Tbo-s/sya_ai-scanner/3D_files/structure/tandwiel(small).stl

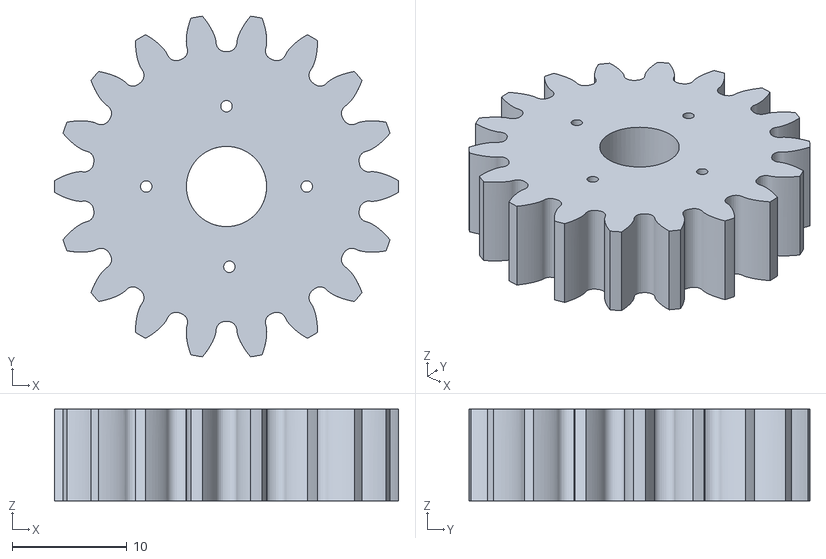
[picture p15: CAD file, 2026-03-24]
3D_files/structure/tandwiel(small).stl
30.0 x 29.7 x 8.00
