Tbo-s/sya_ai-scanner/3D_files/ARM/arm-part3.stl

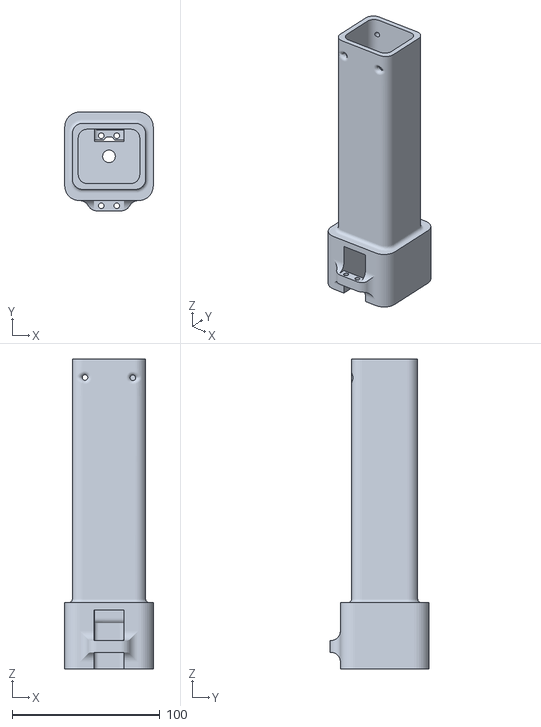
[picture p16: CAD file, 2026-03-13]
3D_files/ARM/arm-part3.stl
60.0 x 67.0 x 210.0
