Tbo-s/sya_ai-scanner/3D_files/gate/gate-motor.stl

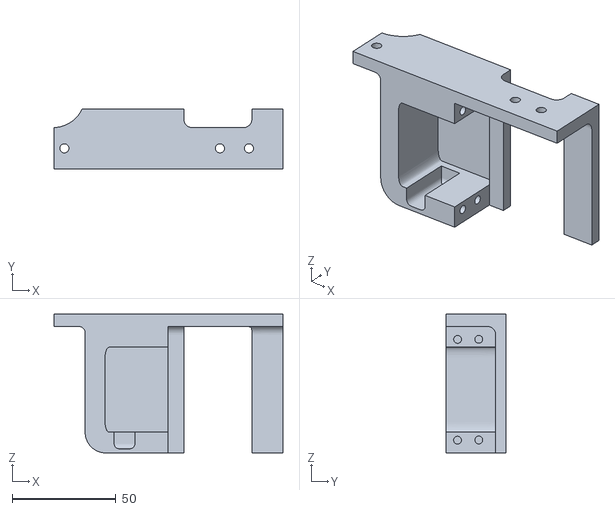
[picture p17: CAD file, 2026-03-03]
3D_files/gate/gate-motor.stl
110.4 x 29.0 x 67.0
