Tbo-s/sya_ai-scanner/3D_files/part-casings/picam.stl

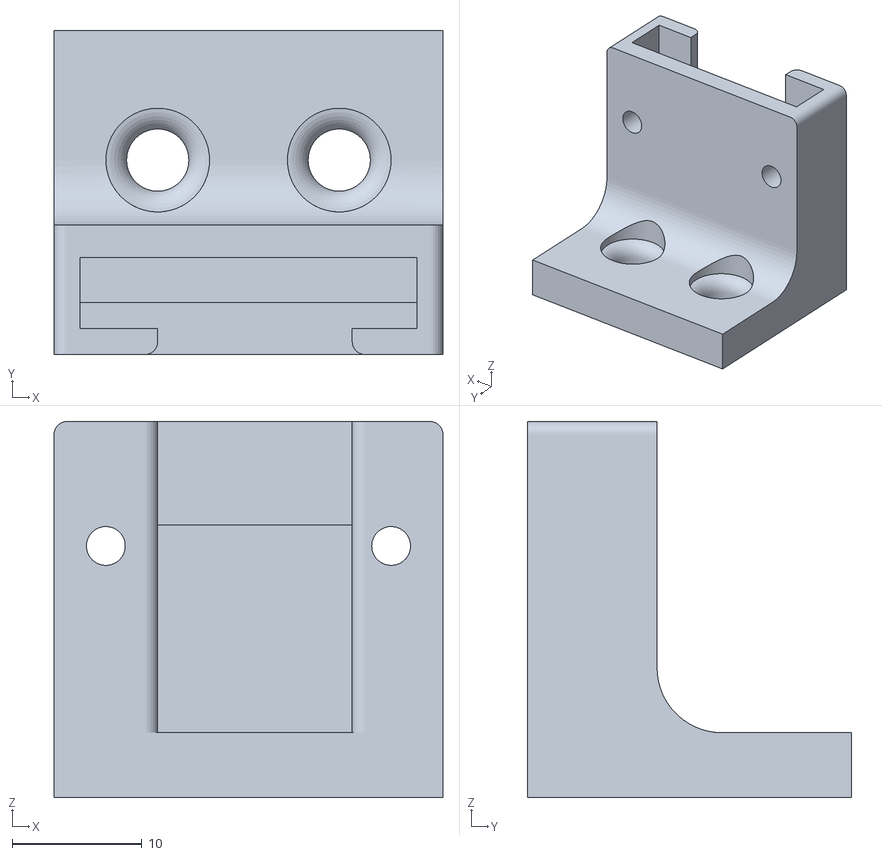
[picture p18: CAD file, 2026-03-13]
3D_files/part-casings/picam.stl
30.0 x 25.0 x 29.0
