Tbo-s/sya_ai-scanner/3D_files/structure/2020brackets.stl

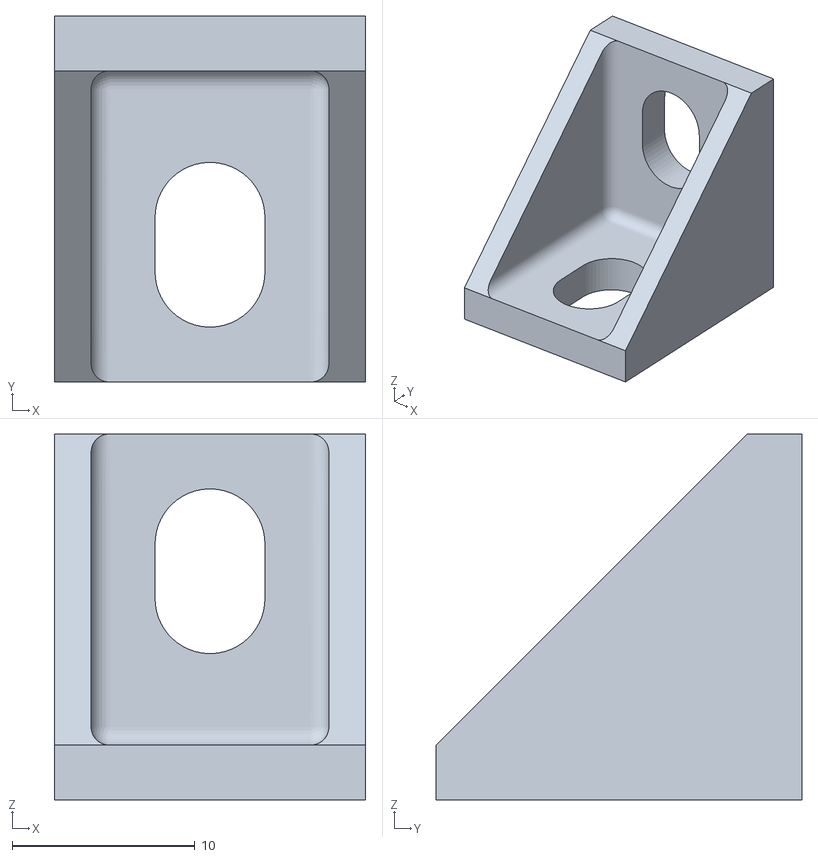
[picture p19: CAD file, 2026-03-09]
3D_files/structure/2020brackets.stl
17.0 x 20.0 x 20.0
