Tbo-s/sya_ai-scanner/3D_files/xy-parts/x-carry3-Right.stl

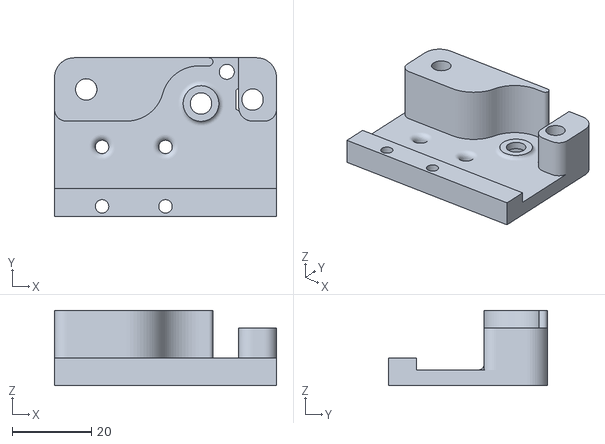
[picture p20: CAD file, 2026-03-04]
3D_files/xy-parts/x-carry3-Right.stl
56.0 x 40.0 x 19.0
