Tbo-s/sya_ai-scanner/3D_files/ARM/arm-part6.stl

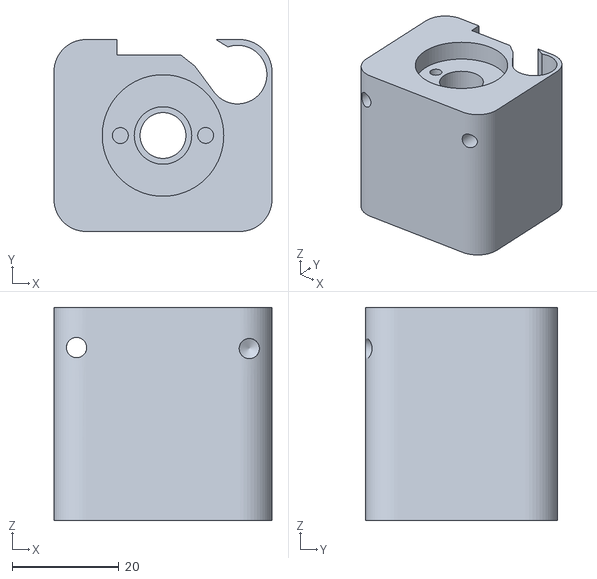
[picture p21: CAD file, 2026-03-03]
3D_files/ARM/arm-part6.stl
40.9 x 36.0 x 40.0
