Tbo-s/sya_ai-scanner/3D_files/gate/gate-part1.stl

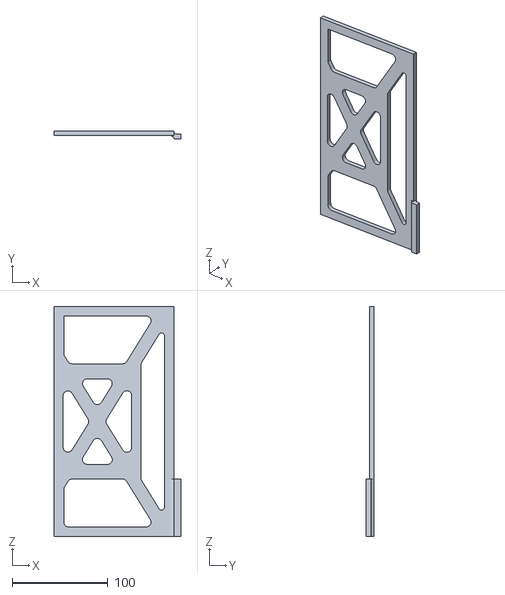
[picture p22: CAD file, 2026-03-03]
3D_files/gate/gate-part1.stl
132.0 x 8.60 x 240.0
