Tbo-s/sya_ai-scanner/3D_files/part-casings/mega_top.stl

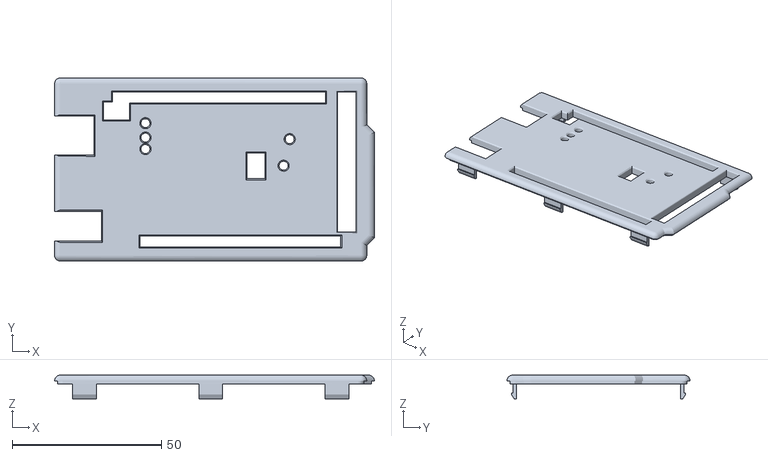
[picture p23: CAD file, 2026-03-10]
3D_files/part-casings/mega_top.stl
107.1 x 61.3 x 8.00
