Tbo-s/sya_ai-scanner/3D_files/structure/LED-holder-right_(3X).stl

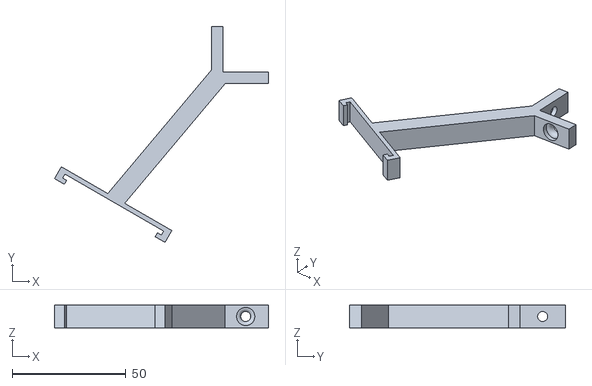
[picture p24: CAD file, 2026-03-03]
3D_files/structure/LED-holder-right_(3X).stl
93.9 x 94.7 x 10.0
