Tbo-s/sya_ai-scanner/3D_files/ARM/arm-part1.stl

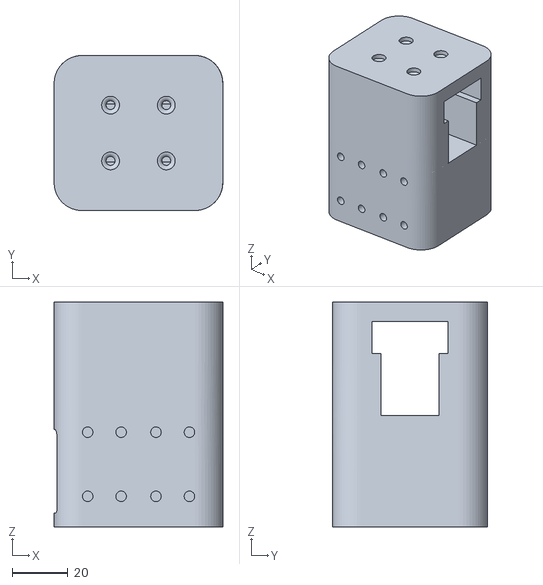
[picture p25: CAD file, 2026-03-03]
3D_files/ARM/arm-part1.stl
60.5 x 55.6 x 80.7
