Tbo-s/sya_ai-scanner/3D_files/part-casings/Leonardo_bottem.stl

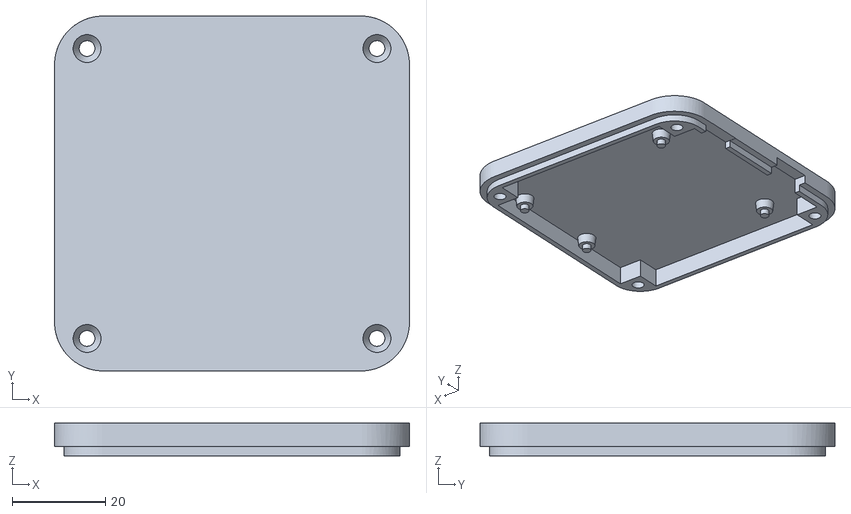
[picture p26: CAD file, 2026-03-10]
3D_files/part-casings/Leonardo_bottem.stl
76.3 x 76.3 x 7.00
