Tbo-s/sya_ai-scanner/3D_files/xy-parts/nema17_holder_right.stl

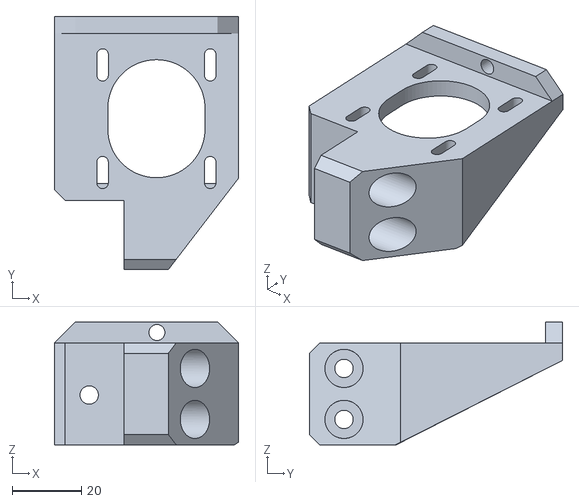
[picture p27: CAD file, 2026-03-03]
3D_files/xy-parts/nema17_holder_right.stl
53.0 x 73.0 x 35.4
