Tbo-s/sya_ai-scanner/3D_files/ARM/arm-part2.stl

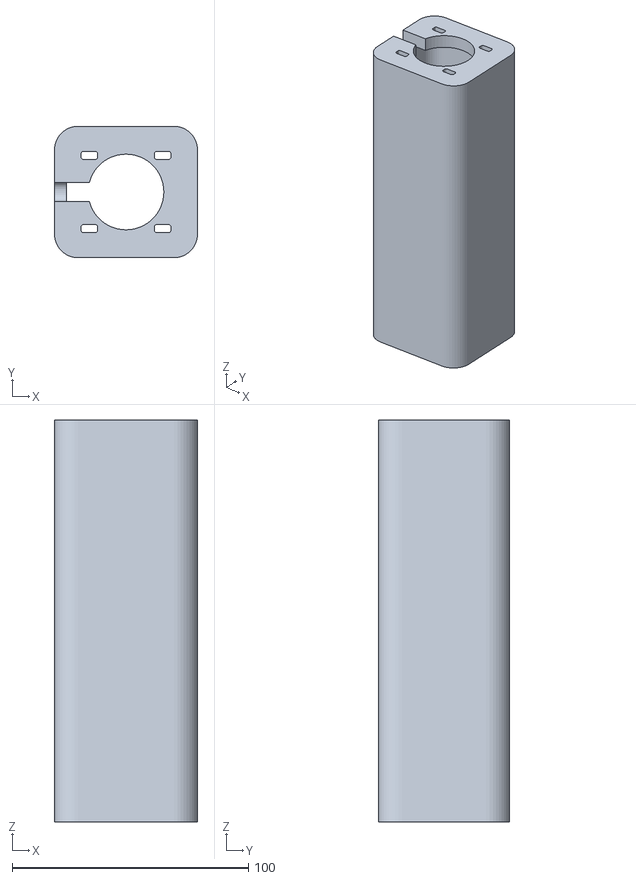
[picture p28: CAD file, 2026-03-03]
3D_files/ARM/arm-part2.stl
60.5 x 55.6 x 170.0
