Tbo-s/sya_ai-scanner/3D_files/gate/gate-part5.stl

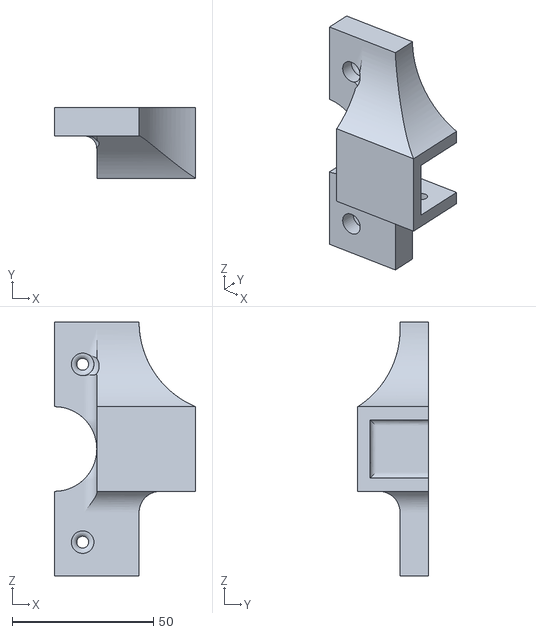
[picture p29: CAD file, 2026-03-03]
3D_files/gate/gate-part5.stl
50.0 x 25.0 x 90.0
