Tbo-s/sya_ai-scanner/3D_files/part-casings/pi_bottem.stl

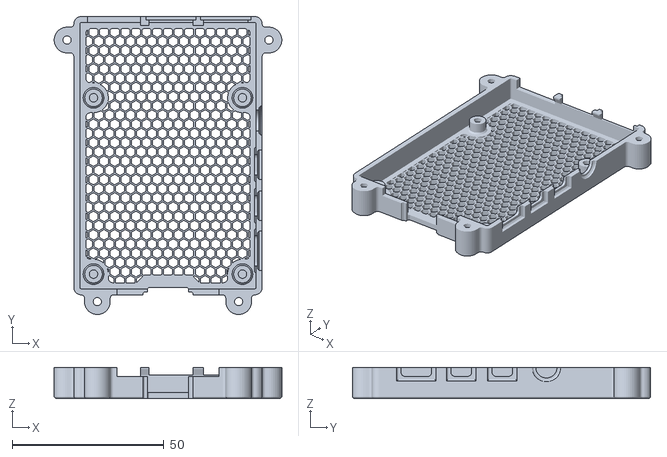
[picture p30: CAD file, 2026-03-10]
3D_files/part-casings/pi_bottem.stl
74.9 x 98.0 x 10.3
