Tbo-s/sya_ai-scanner/3D_files/structure/tandwiel_mg996R_(2X).stl

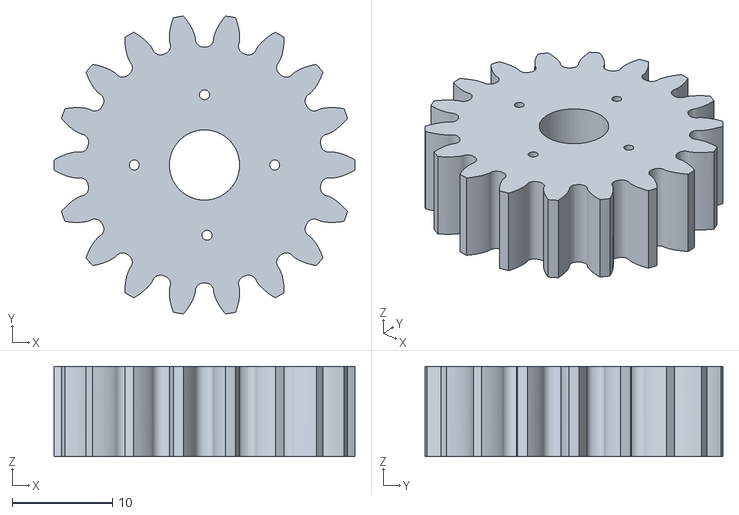
[picture p31: CAD file, 2026-03-03]
3D_files/structure/tandwiel_mg996R_(2X).stl
30.0 x 29.7 x 9.00
