Tbo-s/sya_ai-scanner/3D_files/xy-parts/idler_mount_left.stl

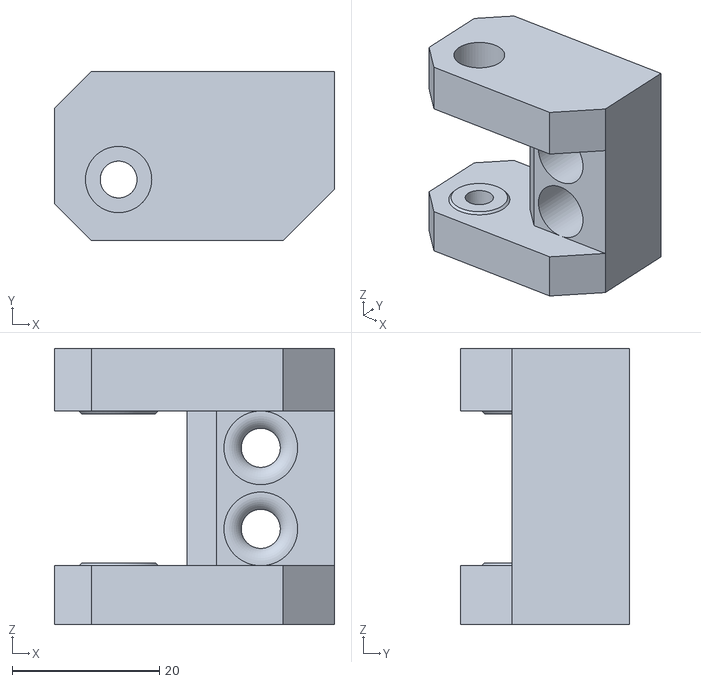
[picture p32: CAD file, 2026-03-03]
3D_files/xy-parts/idler_mount_left.stl
38.0 x 23.0 x 37.5
