Tbo-s/sya_ai-scanner/3D_files/ARM/arm-part7(4X).stl

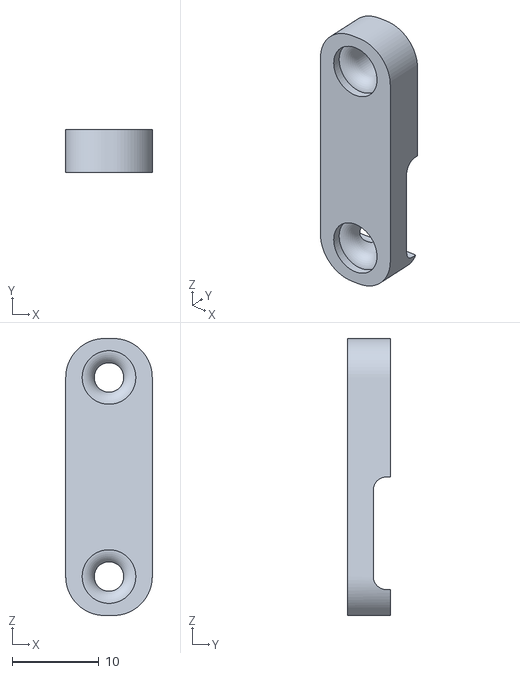
[picture p33: CAD file, 2026-03-03]
3D_files/ARM/arm-part7(4X).stl
10.0 x 5.00 x 32.0
