Tbo-s/sya_ai-scanner/3D_files/gate/gate-motor-adapter.stl

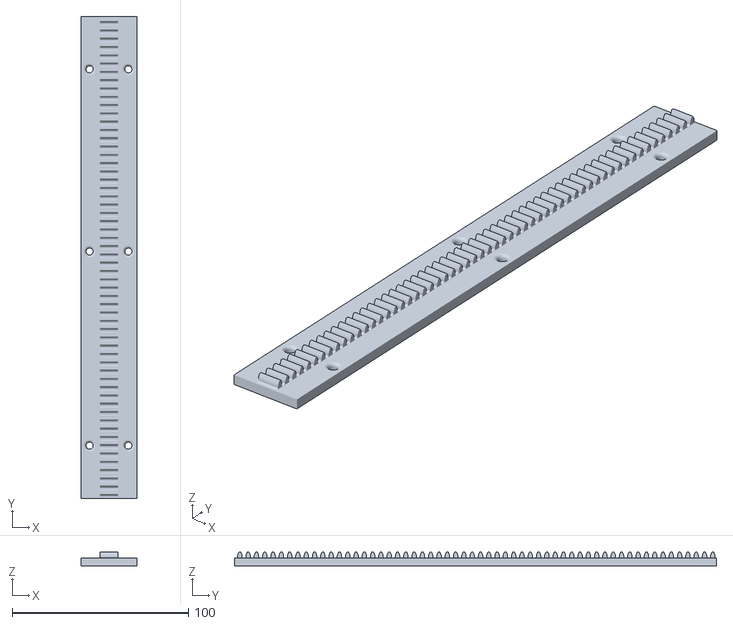
[picture p34: CAD file, 2026-03-03]
3D_files/gate/gate-motor-adapter.stl
32.0 x 273.8 x 7.80
