Tbo-s/sya_ai-scanner/3D_files/part-casings/switch.stl

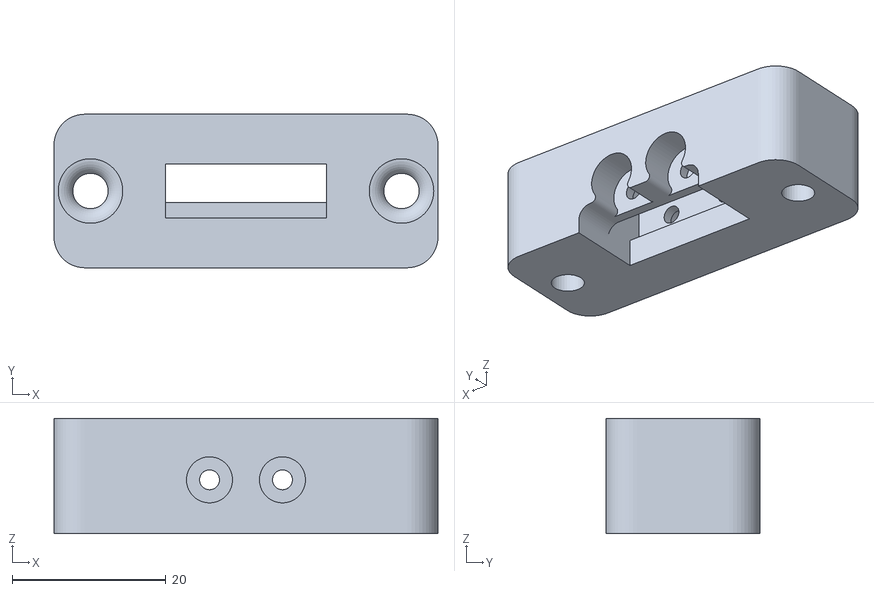
[picture p35: CAD file, 2026-03-10]
3D_files/part-casings/switch.stl
50.0 x 20.0 x 15.0
