Tbo-s/sya_ai-scanner/3D_files/structure/frameconnect_(8X).stl

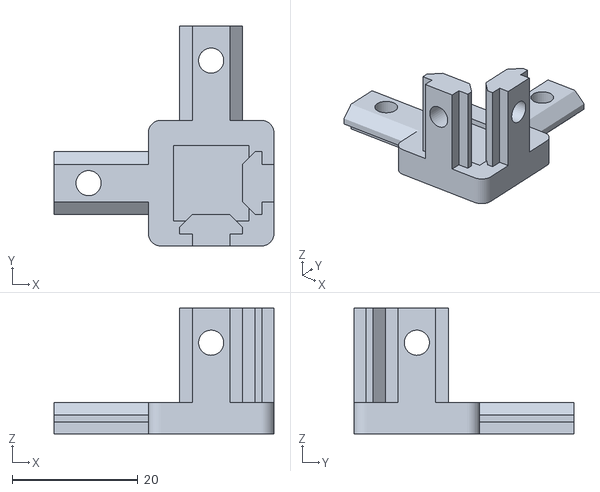
[picture p36: CAD file, 2026-03-03]
3D_files/structure/frameconnect_(8X).stl
35.0 x 35.0 x 20.0
