Tbo-s/sya_ai-scanner/3D_files/part-casings/vacuum-part1-left.stl

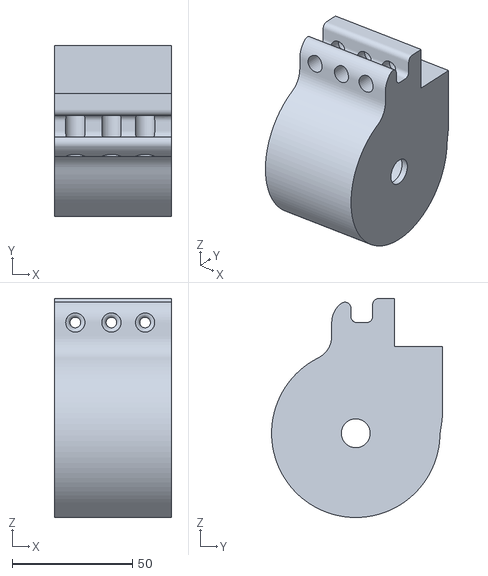
[picture p37: CAD file, 2026-03-09]
3D_files/part-casings/vacuum-part1-left.stl
48.7 x 71.0 x 91.0
