Tbo-s/sya_ai-scanner/3D_files/xy-parts/x-carry2-Left.stl

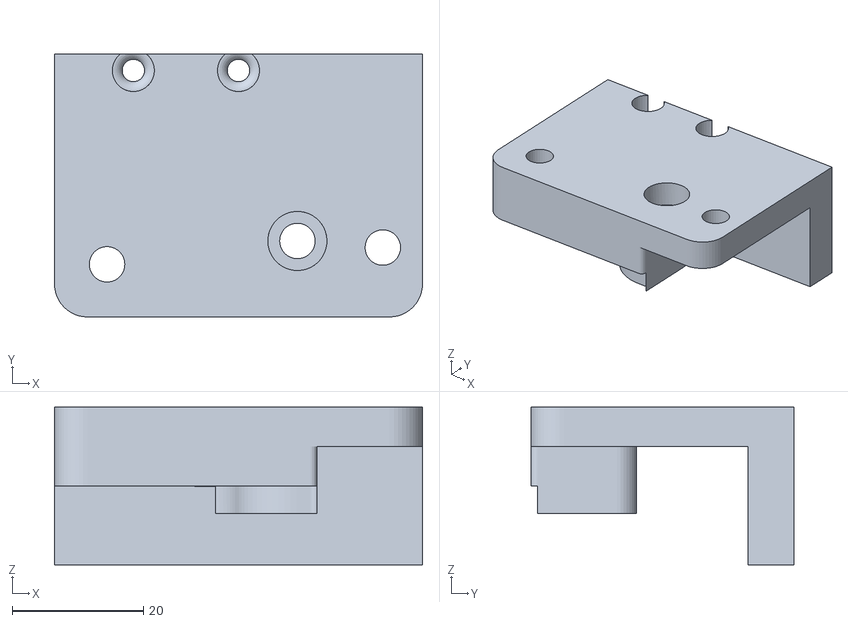
[picture p38: CAD file, 2026-03-03]
3D_files/xy-parts/x-carry2-Left.stl
56.0 x 40.0 x 24.0
