Tbo-s/sya_ai-scanner/3D_files/part-casings/voeding-case.stl

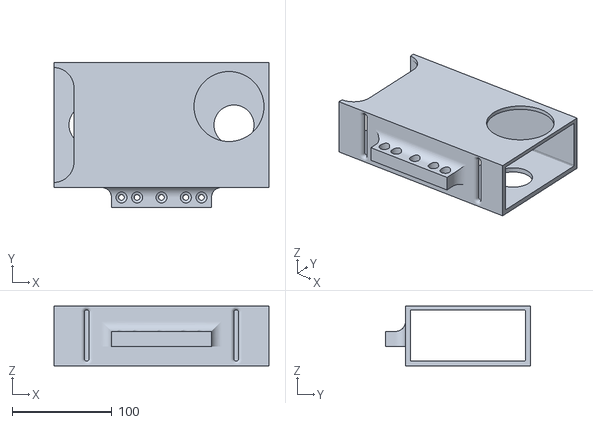
[picture p39: CAD file, 2026-03-09]
3D_files/part-casings/voeding-case.stl
215.0 x 145.0 x 60.0
