Tbo-s/sya_ai-scanner/3D_files/xy-parts/x-carry1-Right.stl

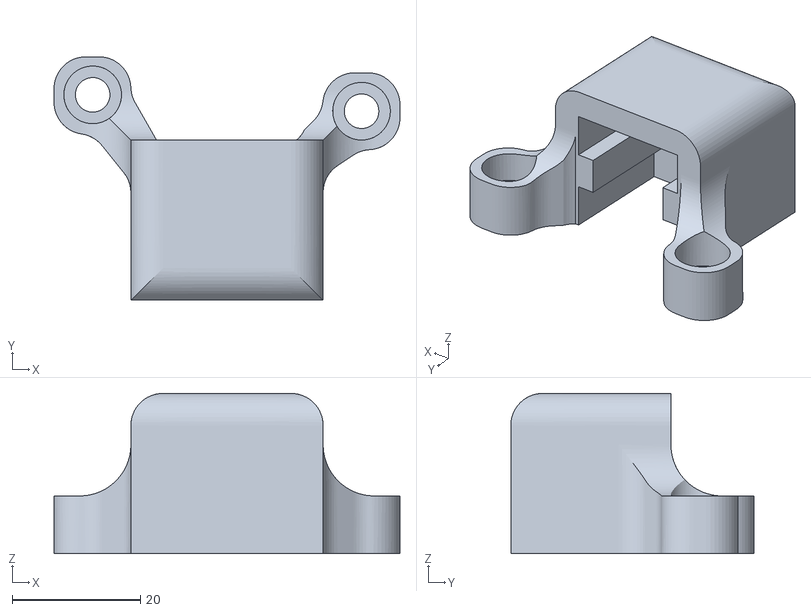
[picture p40: CAD file, 2026-03-03]
3D_files/xy-parts/x-carry1-Right.stl
54.0 x 38.0 x 25.0
