Tbo-s/sya_ai-scanner/3D_files/part-casings/vacuum-part2-left.stl

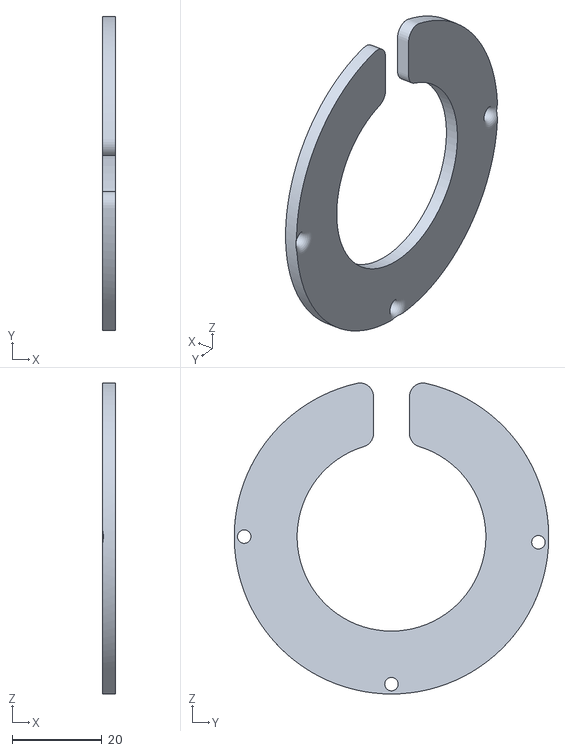
[picture p41: CAD file, 2026-03-03]
3D_files/part-casings/vacuum-part2-left.stl
3.00 x 70.0 x 69.2
