Tbo-s/sya_ai-scanner/code/picode/visionAI/backend/controller/camera.py

from fastapi import APIRouter, HTTPException, Query
from fastapi.responses import Response, StreamingResponse
from pydantic import BaseModel, Field
import os
import re
import shutil
import subprocess
import threading
import time
from datetime import datetime
from pathlib import Path
from typing import Optional

import numpy as np

router = APIRouter()
PI_CAMERA_FULL_WIDTH = 4608
PI_CAMERA_FULL_HEIGHT = 2592
PI_CAMERA_JPEG_QUALITY = 95
PI_CAMERA_AF_TIMEOUT_S = 3.0
PI_CAMERA_STILL_TIMEOUT_EXTRA_S = 10.0
PI_CAMERA_FOCUS_RANGES = {"normal", "macro", "full"}
_PI_CAMERA_FOCUS_CACHE = {"lens_position": None, "expires_at": 0.0}
_PI_CAMERA_FOCUS_CACHE_LOCK = threading.Lock()

try:
    import cv2
except ModuleNotFoundError as exc:
    raise RuntimeError("OpenCV (cv2) is not installed.") from exc


class CameraManager:
    def __init__(self, camera_index: int = 0):
        self.camera_index = camera_index
        self.cap = None
        self.frame = None
        self.lock = threading.Lock()
        self.thread = None
        self.running = False

    def start(self):
        if self.running:
            return
        self.cap = cv2.VideoCapture(self.camera_index)
        if not self.cap.isOpened():
            self.cap.release()
            self.cap = None
            raise HTTPException(status_code=500, detail=f"Could not open camera at index {self.camera_index}.")
        self.running = True
        self.thread = threading.Thread(target=self._reader_loop, daemon=True)
        self.thread.start()

    def _reader_loop(self):
        while self.running and self.cap is not None:
            ok, frame = self.cap.read()
            if ok:
                with self.lock:
                    self.frame = frame
            else:
                time.sleep(0.05)

    def get_frame(self):
        if not self.running:
            self.start()
        with self.lock:
            if self.frame is None:
                return None
            return self.frame.copy()

    def wait_for_frame(self, timeout_s: float = 5.0):
        deadline = time.time() + timeout_s
        while time.time() < deadline:
            frame = self.get_frame()
            if frame is not None:
                return frame
            time.sleep(0.05)
        raise HTTPException(status_code=500, detail="Camera has no frame available.")

    def stop(self):
        self.running = False
        if self.thread:
            self.thread.join(timeout=1)
            self.thread = None
        if self.cap is not None:
            self.cap.release()
            self.cap = None
        with self.lock:
            self.frame = None


def _get_camera_index() -> int:
    return int(os.getenv("APP_CAMERA_INDEX", "0"))


camera_manager = CameraManager(camera_index=_get_camera_index())


class CaptureRequest(BaseModel):
    label: str
    session_id: str


class PiCaptureRequest(BaseModel):
    imei: str = ""
    tag: str = "capture"
    width: int = Field(default=PI_CAMERA_FULL_WIDTH, ge=320, le=5000)
    height: int = Field(default=PI_CAMERA_FULL_HEIGHT, ge=240, le=5000)
    warmup_ms: Optional[int] = Field(default=None, ge=0, le=5000)


class CameraSnapshotSaveRequest(BaseModel):
    tag: str = "camera_view"
    width: int = Field(default=PI_CAMERA_FULL_WIDTH, ge=320, le=5000)
    height: int = Field(default=PI_CAMERA_FULL_HEIGHT, ge=240, le=5000)
    warmup_ms: Optional[int] = Field(default=None, ge=0, le=5000)


def _get_photo_storage_dir() -> Path:
    return Path(os.getenv("APP_PHOTO_STORAGE_DIR", "/tmp/sya_photos"))


def _get_pi_capture_dir() -> Path:
    configured = os.getenv("APP_PI_CAPTURE_DIR", "").strip()
    if configured:
        return Path(configured)
    return Path(__file__).resolve().parent.parent / "data" / "captures"


def _get_camera_capture_dir() -> Path:
    configured = os.getenv("APP_CAMERA_CAPTURE_DIR", "").strip()
    if configured:
        return Path(configured)
    return _get_pi_capture_dir()


def _get_pi_camera_focus_range() -> str:
    focus_range = os.getenv("APP_PI_CAMERA_FOCUS_RANGE", "macro").strip().lower()
    return focus_range if focus_range in PI_CAMERA_FOCUS_RANGES else "macro"


def _get_pi_camera_af_speed() -> str:
    autofocus_speed = os.getenv("APP_PI_CAMERA_AF_SPEED", "normal").strip().lower()
    return autofocus_speed if autofocus_speed in {"normal", "fast"} else "normal"


def _get_pi_camera_af_window() -> str:
    raw = os.getenv("APP_PI_CAMERA_AF_WINDOW", "0.25,0.25,0.5,0.5").strip()
    parts = [part.strip() for part in raw.split(",")]
    if len(parts) != 4:
        return "0.25,0.25,0.5,0.5"
    try:
        values = [min(1.0, max(0.0, float(part))) for part in parts]
    except ValueError:
        return "0.25,0.25,0.5,0.5"
    return ",".join(f"{value:.3f}".rstrip("0").rstrip(".") for value in values)


def _get_pi_camera_lens_position() -> Optional[float]:
    raw = os.getenv("APP_PI_CAMERA_LENS_POSITION", "5.0").strip().lower()
    if raw in {"", "auto", "autofocus", "default"}:
        return None
    try:
        return max(0.0, float(raw))
    except ValueError:
        return 5.0


def _get_pi_camera_warmup_ms() -> int:
    try:
        return min(5000, max(0, int(os.getenv("APP_PI_CAMERA_WARMUP_MS", "1200"))))
    except ValueError:
        return 1200


def _get_pi_camera_focus_settle_ms() -> int:
    try:
        return min(5000, max(0, int(os.getenv("APP_PI_CAMERA_FOCUS_SETTLE_MS", "350"))))
    except ValueError:
        return 350


def _get_pi_camera_close_focus_sweep_enabled() -> bool:
    return os.getenv("APP_PI_CAMERA_CLOSE_FOCUS_SWEEP", "1").strip().lower() in {"1", "true", "yes", "on"}


def _get_pi_camera_focus_cache_ttl_s() -> int:
    try:
        return min(3600, max(0, int(os.getenv("APP_PI_CAMERA_FOCUS_CACHE_TTL_S", "900"))))
    except ValueError:
        return 900


def _get_pi_camera_focus_candidates() -> list[float]:
    raw = os.getenv("APP_PI_CAMERA_FOCUS_CANDIDATES", "2.5,3.5,4.5,5.5,6.5,7.5,9.0,11.0").strip()
    candidates: list[float] = []
    for part in raw.split(","):
        try:
            candidates.append(max(0.0, float(part.strip())))
        except ValueError:
            continue
    return candidates or [2.5, 3.5, 4.5, 5.5, 6.5, 7.5, 9.0, 11.0]


def _normalize_focus_candidates(candidates: list[float]) -> list[float]:
    normalized = sorted({round(max(0.0, value), 3) for value in candidates})
    return normalized or [5.0]


def _build_refined_focus_candidates(best_lens_position: float) -> list[float]:
    return _normalize_focus_candidates(
        [
            best_lens_position - 0.75,
            best_lens_position - 0.5,
            best_lens_position - 0.25,
            best_lens_position,
            best_lens_position + 0.25,
            best_lens_position + 0.5,
            best_lens_position + 0.75,
        ]
    )


def _safe_filename_part(value: str, fallback: str) -> str:
    normalized = re.sub(r"[^A-Za-z0-9_-]+", "_", str(value or "").strip()).strip("_")
    return normalized or fallback


def _wait_for_picamera_job(picam2, job) -> None:
    if job is None:
        return
    if hasattr(picam2, "wait"):
        try:
            picam2.wait(job, timeout=PI_CAMERA_AF_TIMEOUT_S)
            return
        except TypeError:
            picam2.wait(job)
            return
    if hasattr(job, "wait"):
        try:
            job.wait(timeout=PI_CAMERA_AF_TIMEOUT_S)
        except TypeError:
            job.wait()


def _clamp_lens_position_for_camera(picam2, lens_position: float) -> float:
    try:
        lens_control = getattr(picam2, "camera_controls", {}).get("LensPosition")
        if lens_control and len(lens_control) >= 2:
            min_lens = float(lens_control[0])
            max_lens = float(lens_control[1])
            return max(min_lens, min(max_lens, lens_position))
    except Exception:
        pass
    return lens_position


def _set_manual_lens_position(picam2, controls_module, lens_position: float) -> float:
    resolved_lens_position = _clamp_lens_position_for_camera(picam2, lens_position)
    picam2.set_controls(
        {
            "AfMode": controls_module.AfModeEnum.Manual,
            "LensPosition": resolved_lens_position,
        }
    )
    settle_ms = _get_pi_camera_focus_settle_ms()
    if settle_ms > 0:
        time.sleep(settle_ms / 1000.0)
    return resolved_lens_position


def _score_focus_frame(frame) -> float:
    if len(frame.shape) == 2:
        gray = frame
    else:
        gray = cv2.cvtColor(frame, cv2.COLOR_BGR2GRAY)
    height, width = gray.shape[:2]
    crop_height = max(32, int(height * 0.35))
    crop_width = max(32, int(width * 0.35))
    start_y = max(0, (height - crop_height) // 2)
    start_x = max(0, (width - crop_width) // 2)
    crop = gray[start_y:start_y + crop_height, start_x:start_x + crop_width]
    return float(cv2.Laplacian(crop, cv2.CV_64F).var())


def _decode_jpeg_frame(jpeg_bytes: bytes):
    frame = cv2.imdecode(np.frombuffer(jpeg_bytes, dtype=np.uint8), cv2.IMREAD_COLOR)
    if frame is None:
        raise HTTPException(status_code=500, detail="Failed to decode Pi camera JPEG.")
    return frame


def _get_cached_focus_lens_position() -> Optional[float]:
    with _PI_CAMERA_FOCUS_CACHE_LOCK:
        lens_position = _PI_CAMERA_FOCUS_CACHE.get("lens_position")
        expires_at = float(_PI_CAMERA_FOCUS_CACHE.get("expires_at", 0.0) or 0.0)
        if lens_position is None or time.time() >= expires_at:
            return None
        return float(lens_position)


def _set_cached_focus_lens_position(lens_position: float) -> None:
    ttl_s = _get_pi_camera_focus_cache_ttl_s()
    with _PI_CAMERA_FOCUS_CACHE_LOCK:
        _PI_CAMERA_FOCUS_CACHE["lens_position"] = float(lens_position)
        _PI_CAMERA_FOCUS_CACHE["expires_at"] = time.time() + ttl_s if ttl_s > 0 else 0.0


def _capture_pi_frame_with_close_focus_tuning(picam2, controls_module):
    cached_lens_position = _get_cached_focus_lens_position()
    if cached_lens_position is not None:
        _set_manual_lens_position(picam2, controls_module, cached_lens_position)
        return picam2.capture_array("main")

    best_score = -1.0
    best_frame = None
    best_lens_position = None

    def evaluate_candidates(candidates: list[float]) -> None:
        nonlocal best_score, best_frame, best_lens_position
        for lens_position in _normalize_focus_candidates(candidates):
            try:
                resolved_lens_position = _set_manual_lens_position(picam2, controls_module, lens_position)
                frame = picam2.capture_array("main")
                score = _score_focus_frame(cv2.cvtColor(frame, cv2.COLOR_RGB2BGR))
            except Exception:
                continue
            if score > best_score:
                best_score = score
                best_frame = frame
                best_lens_position = resolved_lens_position

    evaluate_candidates(_get_pi_camera_focus_candidates())
    if best_lens_position is not None:
        evaluate_candidates(_build_refined_focus_candidates(best_lens_position))

    if best_frame is not None and best_lens_position is not None:
        _set_cached_focus_lens_position(best_lens_position)
        return best_frame

    _run_pi_autofocus_cycle(picam2, controls_module)
    return picam2.capture_array("main")


def _run_pi_autofocus_cycle(picam2, controls_module) -> None:
    manual_lens_position = _get_pi_camera_lens_position()
    if manual_lens_position is not None:
        try:
            _set_manual_lens_position(picam2, controls_module, manual_lens_position)
            return
        except Exception:
            pass

    focus_controls = {}
    try:
        focus_controls["AfMode"] = controls_module.AfModeEnum.Auto
    except Exception:
        pass

    focus_range_enum = getattr(controls_module, "AfRangeEnum", None)
    if focus_range_enum is not None:
        enum_name = _get_pi_camera_focus_range().capitalize()
        enum_value = getattr(focus_range_enum, enum_name, None)
        if enum_value is not None:
            focus_controls["AfRange"] = enum_value

    focus_speed_enum = getattr(controls_module, "AfSpeedEnum", None)
    if focus_speed_enum is not None:
        enum_name = _get_pi_camera_af_speed().capitalize()
        enum_value = getattr(focus_speed_enum, enum_name, None)
        if enum_value is not None:
            focus_controls["AfSpeed"] = enum_value

    if focus_controls:
        try:
            picam2.set_controls(focus_controls)
        except Exception:
            pass

    autofocus_cycle = getattr(picam2, "autofocus_cycle", None)
    if callable(autofocus_cycle):
        for kwargs in ({"wait": True}, {}):
            try:
                job = autofocus_cycle(**kwargs)
                if not kwargs.get("wait"):
                    _wait_for_picamera_job(picam2, job)
                return
            except TypeError:
                continue
            except Exception:
                return

    try:
        picam2.set_controls({"AfTrigger": controls_module.AfTriggerEnum.Start})
        time.sleep(min(PI_CAMERA_AF_TIMEOUT_S, 1.0))
    except Exception:
        pass


def _capture_pi_csi_frame(width: int, height: int, warmup_ms: int):
    try:
        from picamera2 import Picamera2  # type: ignore
        from libcamera import controls  # type: ignore
    except ModuleNotFoundError as exc:
        raise HTTPException(
            status_code=500,
            detail="Picamera2/libcamera is not installed. On Raspberry Pi install with `sudo apt install -y python3-picamera2`.",
        ) from exc

    picam2 = None
    try:
        picam2 = Picamera2()
        config = picam2.create_still_configuration(main={"size": (width, height)})
        picam2.configure(config)
        picam2.start()
        if warmup_ms > 0:
            time.sleep(warmup_ms / 1000.0)

        if _get_pi_camera_close_focus_sweep_enabled():
            return _capture_pi_frame_with_close_focus_tuning(picam2, controls)

        _run_pi_autofocus_cycle(picam2, controls)
        return picam2.capture_array("main")
    except HTTPException:
        raise
    except Exception as exc:
        raise HTTPException(status_code=500, detail=f"Failed to capture CSI camera frame: {exc}") from exc
    finally:
        if picam2 is not None:
            try:
                picam2.stop()
            except Exception:
                pass
            try:
                picam2.close()
            except Exception:
                pass


def _get_pi_still_command() -> str:
    configured = os.getenv("APP_PI_STILL_COMMAND", "").strip()
    if configured:
        return configured
    for command in ("libcamera-still", "rpicam-still"):
        resolved = shutil.which(command)
        if resolved:
            return resolved
    raise HTTPException(
        status_code=500,
        detail="No Pi camera still command found. Install libcamera/rpicam tools or set APP_PI_STILL_COMMAND.",
    )


def _capture_pi_still_jpeg_with_options(command: str, base_command: list[str], focus_options: list[str], timeout_ms: int) -> bytes:
    candidate = base_command + focus_options
    try:
        completed = subprocess.run(
            candidate,
            check=False,
            stdout=subprocess.PIPE,
            stderr=subprocess.PIPE,
            timeout=(timeout_ms / 1000.0) + PI_CAMERA_STILL_TIMEOUT_EXTRA_S,
        )
    except subprocess.TimeoutExpired as exc:
        raise HTTPException(status_code=504, detail=f"Pi camera still command timed out: {command}") from exc
    except Exception as exc:
        raise HTTPException(status_code=500, detail=f"Failed to run Pi camera still command: {exc}") from exc

    if completed.returncode == 0 and completed.stdout:
        return completed.stdout

    stderr = completed.stderr.decode("utf-8", errors="ignore").strip()
    lowered_stderr = stderr.lower()
    if focus_options and (
        "ambiguous" in lowered_stderr
        or "unrecognised option" in lowered_stderr
        or "unrecognized option" in lowered_stderr
    ):
        raise ValueError("unsupported_focus_option")

    raise HTTPException(
        status_code=500,
        detail=f"Pi camera still command failed: {stderr or 'no output'}",
    )


def _capture_pi_still_jpeg_with_manual_sweep(command: str, base_command: list[str], timeout_ms: int) -> bytes:
    cached_lens_position = _get_cached_focus_lens_position()
    if cached_lens_position is not None:
        for focus_options in (
            ["--autofocus-mode", "manual", "--lens-position", f"{cached_lens_position:.3f}"],
            ["--lens-position", f"{cached_lens_position:.3f}"],
        ):
            try:
                return _capture_pi_still_jpeg_with_options(command, base_command, focus_options, timeout_ms)
            except ValueError:
                continue

    best_score = -1.0
    best_jpeg = None
    best_lens_position = None

    def evaluate_candidates(candidates: list[float]) -> None:
        nonlocal best_score, best_jpeg, best_lens_position
        for lens_position in _normalize_focus_candidates(candidates):
            jpeg_bytes = None
            for focus_options in (
                ["--autofocus-mode", "manual", "--lens-position", f"{lens_position:.3f}"],
                ["--lens-position", f"{lens_position:.3f}"],
            ):
                try:
                    jpeg_bytes = _capture_pi_still_jpeg_with_options(command, base_command, focus_options, timeout_ms)
                    break
                except ValueError:
                    continue
            if jpeg_bytes is None:
                continue
            try:
                score = _score_focus_frame(_decode_jpeg_frame(jpeg_bytes))
            except Exception:
                continue
            if score > best_score:
                best_score = score
                best_jpeg = jpeg_bytes
                best_lens_position = lens_position

    evaluate_candidates(_get_pi_camera_focus_candidates())
    if best_lens_position is not None:
        evaluate_candidates(_build_refined_focus_candidates(best_lens_position))

    if best_jpeg is not None and best_lens_position is not None:
        _set_cached_focus_lens_position(best_lens_position)
        return best_jpeg

    raise HTTPException(status_code=500, detail="Pi camera focus sweep did not produce a valid image.")


def _capture_pi_still_jpeg(width: int, height: int, warmup_ms: int) -> bytes:
    command = _get_pi_still_command()
    focus_range = _get_pi_camera_focus_range()
    focus_speed = _get_pi_camera_af_speed()
    focus_window = _get_pi_camera_af_window()
    manual_lens_position = _get_pi_camera_lens_position()
    timeout_ms = max(warmup_ms, 2000)
    base_command = [
        command,
        "--nopreview",
        "--output",
        "-",
        "--width",
        str(width),
        "--height",
        str(height),
        "--quality",
        str(PI_CAMERA_JPEG_QUALITY),
        "--timeout",
        str(timeout_ms),
    ]

    if _get_pi_camera_close_focus_sweep_enabled():
        try:
            return _capture_pi_still_jpeg_with_manual_sweep(command, base_command, timeout_ms)
        except HTTPException:
            pass

    autofocus_options: list[list[str]] = []
    full_autofocus_options = ["--autofocus-mode", "auto", "--autofocus-range", focus_range, "--autofocus-speed", focus_speed]
    if focus_window:
        full_autofocus_options.extend(["--autofocus-window", focus_window])
    autofocus_options.append(full_autofocus_options + ["--autofocus-on-capture"])
    autofocus_options.append(full_autofocus_options)
    autofocus_options.append(["--autofocus-on-capture", "--autofocus-range", focus_range, "--autofocus-speed", focus_speed])
    autofocus_options.append(["--autofocus-range", focus_range, "--autofocus-speed", focus_speed])
    autofocus_options.append(["--autofocus-range", focus_range])
    autofocus_options.append([])

    focus_candidates = tuple(autofocus_options)
    if manual_lens_position is not None:
        focus_candidates = (
            ["--autofocus-mode", "manual", "--lens-position", f"{manual_lens_position:.3f}"],
            ["--lens-position", f"{manual_lens_position:.3f}"],
            *focus_candidates,
        )

    for focus_options in focus_candidates:
        try:
            return _capture_pi_still_jpeg_with_options(command, base_command, focus_options, timeout_ms)
        except ValueError:
            continue

    raise HTTPException(status_code=500, detail="Pi camera still command failed.")


def _capture_pi_csi_jpeg(width: int, height: int, warmup_ms: int) -> bytes:
    picamera_error = None
    try:
        frame = _capture_pi_csi_frame(width, height, warmup_ms)
        return _encode_jpeg(cv2.cvtColor(frame, cv2.COLOR_RGB2BGR))
    except HTTPException as exc:
        picamera_error = exc.detail

    try:
        return _capture_pi_still_jpeg(width, height, warmup_ms)
    except HTTPException as exc:
        raise HTTPException(
            status_code=exc.status_code,
            detail={
                "picamera2": picamera_error,
                "still_command": exc.detail,
            },
        ) from exc


def _extract_imei_from_text(text: str):
    digits_only = re.sub(r"\D", "", text)
    match = re.search(r"\d{15}", digits_only)
    if match:
        return match.group(0)
    return None


def _mjpeg_stream():
    while True:
        frame = camera_manager.get_frame()
        if frame is None:
            time.sleep(0.05)
            continue
        ok, jpg = cv2.imencode(".jpg", frame)
        if not ok:
            continue
        payload = jpg.tobytes()
        yield (
            b"--frame\r\n"
            b"Content-Type: image/jpeg\r\n"
            + f"Content-Length: {len(payload)}\r\n\r\n".encode("utf-8")
            + payload
            + b"\r\n"
        )


@router.get("/camera/stream", tags=["Camera"])
def camera_stream():
    camera_manager.start()
    return StreamingResponse(_mjpeg_stream(), media_type="multipart/x-mixed-replace; boundary=frame")


@router.get("/imei/detect", tags=["Camera"])
def detect_imei():
    try:
        from pyzbar.pyzbar import decode
    except ModuleNotFoundError as exc:
        raise HTTPException(
            status_code=500,
            detail="pyzbar is not installed. Install with `pip install pyzbar` and `sudo apt install libzbar0`.",
        ) from exc

    frame = camera_manager.get_frame()
    if frame is None:
        return {"found": False, "detail": "No frame available yet."}
    gray = cv2.cvtColor(frame, cv2.COLOR_BGR2GRAY)
    decoded_objects = decode(gray) or decode(frame)
    for obj in decoded_objects:
        try:
            raw_text = obj.data.decode("utf-8")
        except Exception:
            continue
        imei = _extract_imei_from_text(raw_text)
        if imei:
            return {"found": True, "imei": imei, "raw": raw_text, "type": obj.type}
    return {"found": False}


def take_photo(label: str, session_id: str) -> dict:
    frame = camera_manager.wait_for_frame()
    session_dir = _get_photo_storage_dir() / session_id
    session_dir.mkdir(parents=True, exist_ok=True)
    file_path = session_dir / f"{label}.jpg"
    ok, jpg = cv2.imencode(".jpg", frame)
    if not ok:
        raise HTTPException(status_code=500, detail="Failed to encode camera frame as JPEG.")
    file_path.write_bytes(jpg.tobytes())
    return {"path": str(file_path), "label": label, "session_id": session_id}


def _encode_jpeg(frame) -> bytes:
    ok, jpg = cv2.imencode(".jpg", frame, [int(cv2.IMWRITE_JPEG_QUALITY), PI_CAMERA_JPEG_QUALITY])
    if not ok:
        raise HTTPException(status_code=500, detail="Failed to encode camera frame as JPEG.")
    return jpg.tobytes()


def _encode_jpeg_response(frame) -> Response:
    return Response(
        content=_encode_jpeg(frame),
        media_type="image/jpeg",
        headers={"Cache-Control": "no-store"},
    )


@router.get("/camera/snapshot/{source}", tags=["Camera"])
def camera_snapshot(
    source: str,
    width: int = Query(default=PI_CAMERA_FULL_WIDTH, ge=320, le=5000),
    height: int = Query(default=PI_CAMERA_FULL_HEIGHT, ge=240, le=5000),
    warmup_ms: Optional[int] = Query(default=None, ge=0, le=5000),
):
    normalized = source.strip().lower()
    resolved_warmup_ms = _get_pi_camera_warmup_ms() if warmup_ms is None else warmup_ms
    if normalized == "usb":
        camera_manager.start()
        return _encode_jpeg_response(camera_manager.wait_for_frame())
    if normalized == "pi":
        return Response(
            content=_capture_pi_csi_jpeg(width, height, resolved_warmup_ms),
            media_type="image/jpeg",
            headers={"Cache-Control": "no-store"},
        )
    raise HTTPException(status_code=400, detail="Unknown camera source. Use 'usb' or 'pi'.")


@router.post("/camera/snapshot/{source}/save", tags=["Camera"])
def save_camera_snapshot(source: str, payload: CameraSnapshotSaveRequest):
    normalized = source.strip().lower()
    resolved_warmup_ms = _get_pi_camera_warmup_ms() if payload.warmup_ms is None else payload.warmup_ms
    if normalized == "usb":
        camera_manager.start()
        jpeg_bytes = _encode_jpeg(camera_manager.wait_for_frame())
    elif normalized == "pi":
        jpeg_bytes = _capture_pi_csi_jpeg(payload.width, payload.height, resolved_warmup_ms)
    else:
        raise HTTPException(status_code=400, detail="Unknown camera source. Use 'usb' or 'pi'.")

    capture_dir = _get_camera_capture_dir()
    capture_dir.mkdir(parents=True, exist_ok=True)
    source_part = _safe_filename_part(normalized, "camera")
    tag_part = _safe_filename_part(payload.tag, "camera_view")
    timestamp = datetime.utcnow().strftime("%Y%m%d_%H%M%S_%f")
    filename = f"{timestamp}_{source_part}_{tag_part}.jpg"
    file_path = capture_dir / filename
    file_path.write_bytes(jpeg_bytes)
    return {
        "saved": True,
        "source": normalized,
        "tag": payload.tag,
        "filename": filename,
        "path": str(file_path),
    }


@router.post("/camera/capture", tags=["Camera"])
def capture_photo(payload: CaptureRequest):
    camera_manager.start()
    return take_photo(payload.label, payload.session_id)


@router.post("/camera/pi/capture", tags=["Camera"])
def capture_pi_camera_photo(payload: PiCaptureRequest):
    capture_dir = _get_pi_capture_dir()
    capture_dir.mkdir(parents=True, exist_ok=True)
    imei_part = _safe_filename_part(payload.imei, "no_imei")
    tag_part = _safe_filename_part(payload.tag, "capture")
    timestamp = datetime.utcnow().strftime("%Y%m%d_%H%M%S_%f")
    filename = f"{timestamp}_{imei_part}_{tag_part}.jpg"
    file_path = capture_dir / filename
    resolved_warmup_ms = _get_pi_camera_warmup_ms() if payload.warmup_ms is None else payload.warmup_ms
    file_path.write_bytes(_capture_pi_csi_jpeg(payload.width, payload.height, resolved_warmup_ms))
    return {"saved": True, "filename": filename, "path": str(file_path), "imei": payload.imei, "tag": payload.tag}
