Tbo-s/sya_ai-scanner/code/picode/visionAI/backend/tests/test_machine_service.py

from services import machine_service
from services.machine_service import (
    _derive_tray_position_from_status,
    _extract_gate_position,
    _extract_status_line,
    _get_status_values,
    _parse_status_values,
)


def test_extract_gate_position_from_lines():
    assert _extract_gate_position(["foo", "GATE_POS=UP"]) == "UP"
    assert _extract_gate_position(["foo", "ACK:GATE_POS=DOWN"]) == "DOWN"


def test_extract_status_line_finds_latest_status():
    lines = [
        "Leonardo ready",
        "gateState=1, gatePos=UP, trayState=0, gateOpenSw=1, gateCloseSw=0, trayOutSw=0, trayInSw=1",
        "noise",
    ]
    status = _extract_status_line(lines)
    assert status is not None
    assert status.startswith("gateState=")


def test_extract_status_line_strips_ack_prefix():
    lines = [
        "READY:LEONARDO",
        "ACK:STATUS,gateState=0,gatePos=DOWN,trayState=0,trayPos=IN,wrist1=90,wrist2=90,distanceMm=123,gateOpenSw=0,gateCloseSw=1,trayOutSw=0,trayInSw=1",
    ]
    status = _extract_status_line(lines)
    assert status == (
        "gateState=0,gatePos=DOWN,trayState=0,trayPos=IN,wrist1=90,wrist2=90,"
        "distanceMm=123,gateOpenSw=0,gateCloseSw=1,trayOutSw=0,trayInSw=1"
    )


def test_parse_status_values():
    status_line = "gateState=0, gatePos=DOWN, trayState=2, gateOpenSw=0, gateCloseSw=1, trayOutSw=1, trayInSw=0"
    values = _parse_status_values(status_line)
    assert values["gatePos"] == "DOWN"
    assert values["trayOutSw"] == "1"


def test_parse_status_values_keeps_distance_mm():
    status_line = (
        "gateState=0, gatePos=DOWN, trayState=0, trayPos=IN, wrist1=90, wrist2=90, "
        "vac1=0, vac2=0, valve1=0, valve2=0, distanceMm=123, "
        "gateOpenSw=0, gateCloseSw=1, trayOutSw=0, trayInSw=1"
    )

    status = _extract_status_line([status_line])
    values = _parse_status_values(status or "")

    assert status == status_line
    assert values["distanceMm"] == "123"
    assert values["trayInSw"] == "1"


def test_get_status_values_retries_until_parseable(monkeypatch):
    responses = [
        ["READY:LEONARDO"],
        [
            "ACK:STATUS,gateState=0,gatePos=DOWN,trayState=0,trayPos=IN,"
            "wrist1=90,wrist2=90,vac1=0,vac2=0,valve1=0,valve2=0,"
            "distanceMm=123,gateOpenSw=0,gateCloseSw=1,trayOutSw=0,trayInSw=1"
        ],
    ]

    def fake_send_with_response(command, **_kwargs):
        assert command == "STATUS"
        return responses.pop(0)

    monkeypatch.setenv("APP_LEONARDO_STATUS_RETRIES", "2")
    monkeypatch.setenv("APP_LEONARDO_STATUS_RETRY_DELAY_S", "0")
    monkeypatch.setattr(machine_service, "_send_with_response", fake_send_with_response)

    values, lines = _get_status_values()

    assert values["distanceMm"] == "123"
    assert values["trayInSw"] == "1"
    assert lines[0] == "READY:LEONARDO"


def test_derive_tray_position_out():
    position = _derive_tray_position_from_status({"trayOutSw": "1", "trayInSw": "0"})
    assert position == "OUT"


def test_derive_tray_position_in():
    position = _derive_tray_position_from_status({"trayOutSw": "0", "trayInSw": "1"})
    assert position == "IN"


def test_derive_tray_position_unknown():
    position = _derive_tray_position_from_status({"trayOutSw": "1", "trayInSw": "1"})
    assert position == "UNKNOWN"


def test_vacuum_motor_waits_for_ack(monkeypatch):
    sent_commands = []

    def fake_send_with_response(command, **_kwargs):
        sent_commands.append(command)
        return [f"ACK:{command}"]

    monkeypatch.setattr(machine_service, "_send_with_response", fake_send_with_response)

    result = machine_service.set_vacuum1_motor(True)

    assert sent_commands == ["VAC1_ON"]
    assert result["ack"] is True
    assert result["enabled"] is True
    assert result["response"] == ["ACK:VAC1_ON"]
