Tbo-s/sya_ai-scanner/code/picode/visionAI/backend/tests/test_grbl_service.py

import pytest

import services.grbl_service as grbl_service
from services.grbl_service import (
    _parse_sequence,
    home_axes_to_limits,
    home_axes_x_y_z_to_limits,
    is_safe_grbl_command,
    manual_z_down,
    manual_z_up,
    z_down,
    z_up,
)


def test_grbl_allows_basic_command():
    assert is_safe_grbl_command("G0 X10.0 Y-5 F300")


def test_grbl_rejects_empty_command():
    assert not is_safe_grbl_command("   ")


def test_grbl_rejects_unsafe_shell_chars():
    assert not is_safe_grbl_command("G0 X10; rm -rf /")


def test_parse_sequence_pipe_separator():
    assert _parse_sequence("$X|$H") == ["$X", "$H"]


def test_parse_sequence_semicolon_separator():
    assert _parse_sequence("$X;$H") == ["$X", "$H"]


def test_parse_sequence_filters_empty_parts():
    assert _parse_sequence(" $X || ; $H ") == ["$X", "$H"]


def test_parse_grbl_status_line_extracts_coordinates_and_limits():
    grbl_service._set_arm_unhomed()
    status = grbl_service._parse_grbl_status_line("<Idle|MPos:1.000,2.000,3.000|WPos:0.500,1.500,0.000|Pn:XYZ>")

    assert status is not None
    assert status["state"] == "Idle"
    assert status["machine_position"] == {"x": 1.0, "y": 2.0, "z": 3.0}
    assert status["work_position"] == {"x": 0.5, "y": 1.5, "z": 0.0}
    assert status["limits"] == {"x": True, "y": True, "z": True}
    assert status["limit_axes"] == ["x", "y", "z"]


def test_parse_grbl_status_line_supports_active_absent_limit_pins(monkeypatch):
    monkeypatch.setenv("APP_GRBL_LIMIT_PIN_MODE", "active_absent")

    status = grbl_service._parse_grbl_status_line("<Idle|MPos:1.000,2.000,3.000|Pn:XYZ>")
    assert status is not None
    assert status["limits"] == {"x": False, "y": False, "z": False}

    status = grbl_service._parse_grbl_status_line("<Idle|MPos:1.000,2.000,3.000|Pn:XY>")
    assert status is not None
    assert status["limits"] == {"x": False, "y": False, "z": True}

    status = grbl_service._parse_grbl_status_line("<Idle|MPos:1.000,2.000,3.000>")
    assert status is not None
    assert status["limits"] == {"x": False, "y": False, "z": False}


def test_limit_stop_axes_use_configured_zero_direction(monkeypatch):
    monkeypatch.setenv("APP_GRBL_X_LIMIT_TOWARD_ZERO_SIGN", "1")
    monkeypatch.setenv("APP_GRBL_Y_LIMIT_TOWARD_ZERO_SIGN", "-1")

    assert grbl_service._limit_stop_axes_for_xy_delta(1.0, -1.0) == {"x", "y"}
    assert grbl_service._limit_stop_axes_for_xy_delta(-1.0, 1.0) == set()


def test_z_up_uses_absolute_positioning(monkeypatch):
    commands = []
    wait_flags = []

    def fake_run_grbl_commands(sequence, wait_for_idle=False, settle_delay_s=0.0, **kwargs):
        commands.extend(sequence)
        wait_flags.append(wait_for_idle)
        return [{"command": command, "wait_for_ok": wait_for_ok} for command, wait_for_ok in sequence]

    monkeypatch.setenv("APP_GRBL_Z_AXIS_ENABLED", "1")
    monkeypatch.setenv("APP_GRBL_Z_PICKUP", "42.5")
    monkeypatch.setenv("APP_GRBL_FEED_RATE", "1234")
    monkeypatch.setattr(grbl_service, "_run_grbl_commands", fake_run_grbl_commands)

    result = z_up()

    assert result["action"] == "z_up"
    assert commands == [("G21", True), ("G90", True), ("G1 Z42.5 F1234", True)]
    assert wait_flags == [False]


def test_z_down_uses_absolute_positioning(monkeypatch):
    commands = []
    wait_flags = []

    def fake_run_grbl_commands(sequence, wait_for_idle=False, settle_delay_s=0.0, **kwargs):
        commands.extend(sequence)
        wait_flags.append(wait_for_idle)
        return [{"command": command, "wait_for_ok": wait_for_ok} for command, wait_for_ok in sequence]

    monkeypatch.setenv("APP_GRBL_Z_AXIS_ENABLED", "1")
    monkeypatch.setenv("APP_GRBL_Z_TRAVEL", "7.0")
    monkeypatch.setenv("APP_GRBL_FEED_RATE", "900")
    monkeypatch.setattr(grbl_service, "_run_grbl_commands", fake_run_grbl_commands)

    result = z_down()

    assert result["action"] == "z_down"
    assert commands == [("G21", True), ("G90", True), ("G1 Z7.0 F900", True)]
    assert wait_flags == [False]


def test_manual_z_up_uses_relative_jog_and_slow_feed(monkeypatch):
    commands = []
    wait_flags = []

    def fake_run_grbl_commands(sequence, wait_for_idle=False, settle_delay_s=0.0):
        commands.extend(sequence)
        wait_flags.append(wait_for_idle)
        return [{"command": command, "wait_for_ok": wait_for_ok} for command, wait_for_ok in sequence]

    monkeypatch.setenv("APP_GRBL_Z_AXIS_ENABLED", "1")
    monkeypatch.setenv("APP_GRBL_MANUAL_Z_STEP", "1.25")
    monkeypatch.setenv("APP_GRBL_MANUAL_Z_FEED_RATE", "90")
    monkeypatch.setattr(grbl_service, "_run_grbl_commands", fake_run_grbl_commands)

    result = manual_z_up()

    assert result["action"] == "manual_z_up"
    assert commands == [("G21", True), ("G91", True), ("G1 Z1.25 F90", True), ("G90", True)]
    assert wait_flags == [True]


def test_manual_z_down_uses_relative_jog_and_slow_feed(monkeypatch):
    commands = []
    wait_flags = []

    def fake_run_grbl_commands(sequence, wait_for_idle=False, settle_delay_s=0.0):
        commands.extend(sequence)
        wait_flags.append(wait_for_idle)
        return [{"command": command, "wait_for_ok": wait_for_ok} for command, wait_for_ok in sequence]

    monkeypatch.setenv("APP_GRBL_Z_AXIS_ENABLED", "1")
    monkeypatch.setenv("APP_GRBL_MANUAL_Z_STEP", "0.75")
    monkeypatch.setenv("APP_GRBL_MANUAL_Z_FEED_RATE", "60")
    monkeypatch.setattr(grbl_service, "_run_grbl_commands", fake_run_grbl_commands)

    result = manual_z_down()

    assert result["action"] == "manual_z_down"
    assert commands == [("G21", True), ("G91", True), ("G1 Z-0.75 F60", True), ("G90", True)]
    assert wait_flags == [True]


def test_manual_z_move_is_skipped_when_z_axis_disabled(monkeypatch):
    calls = []

    monkeypatch.setenv("APP_GRBL_Z_AXIS_ENABLED", "0")
    monkeypatch.setattr(grbl_service, "_run_grbl_commands", lambda *args, **kwargs: calls.append("move") or [])

    result = grbl_service.manual_z_move(5.0)

    assert result["action"] == "manual_z_move"
    assert result["skipped"] is True
    assert result["disabled"] is True
    assert result["reason"] == "z_axis_disabled"
    assert calls == []


def test_home_z_axis_steps_down_until_z_limit(monkeypatch):
    calls = []

    def fake_run_grbl_commands(sequence, wait_for_idle=False, **kwargs):
        calls.append({"sequence": sequence, "wait_for_idle": wait_for_idle, "kwargs": kwargs})
        if kwargs.get("observe_limit_axes") == {"z"} and len(calls) == 3:
            return [{"idle": {"limit_triggered": True, "limit_axes": ["z"]}}]
        return [{"command": command, "wait_for_ok": wait_for_ok} for command, wait_for_ok in sequence]

    monkeypatch.setenv("APP_GRBL_Z_AXIS_ENABLED", "1")
    monkeypatch.setenv("APP_GRBL_HOME_Z_STEP", "1.0")
    monkeypatch.setenv("APP_GRBL_HOME_Z_SEARCH_DISTANCE", "5.0")
    monkeypatch.setenv("APP_GRBL_HOME_Z_FEED_RATE", "30")
    monkeypatch.setattr(
        grbl_service,
        "_read_homing_limit_precheck",
        lambda: {"limits": {"x": False, "y": False, "z": False}},
    )
    monkeypatch.setattr(grbl_service, "_run_grbl_commands", fake_run_grbl_commands)

    result = grbl_service._home_z_axis()

    assert result["stopped_by_limit"] is True
    assert result["steps"] == 3
    assert [
        call["sequence"][2]
        for call in calls
    ] == [("G1 Z-1.0 F30", True), ("G1 Z-1.0 F30", True), ("G1 Z-1.0 F30", True)]


def test_home_axes_to_limits_runs_z_clearance_before_xy_then_z(monkeypatch):
    calls = []

    monkeypatch.setenv("APP_GRBL_Z_AXIS_ENABLED", "1")
    monkeypatch.setattr(grbl_service, "_unlock_grbl_if_needed", lambda: calls.append("unlock") or {"command": "$X"})
    monkeypatch.setattr(grbl_service, "ensure_nc_limit_pin_setting", lambda: calls.append("limits") or {"configured": False})
    monkeypatch.setattr(
        grbl_service,
        "_read_homing_limit_precheck",
        lambda: calls.append("precheck") or {"limits": {"x": False, "y": False, "z": False}},
    )
    monkeypatch.setattr(grbl_service, "_home_z_clearance", lambda: calls.append("z_clearance") or {"axis": "z"})
    monkeypatch.setattr(grbl_service, "_get_home_xy_axis_order", lambda: ["x", "y"])
    monkeypatch.setattr(
        grbl_service,
        "_home_xy_axis",
        lambda axis, precheck_status=None: calls.append(f"xy_{axis}") or {"axis": axis},
    )
    monkeypatch.setattr(
        grbl_service,
        "_home_z_axis",
        lambda precheck_status=None: calls.append("z_home") or {"axis": "z"},
    )
    monkeypatch.setattr(grbl_service, "_zero_work_position", lambda include_z: calls.append(f"zero_{include_z}") or [])

    result = home_axes_to_limits()

    assert calls == [
        "unlock",
        "limits",
        "precheck",
        "z_clearance",
        "xy_x",
        "xy_y",
        "precheck",
        "z_home",
        "zero_True",
    ]
    assert result["action"] == "home_axes_to_limits"
    assert result["sequence"] == ["z_clearance", "home_xy", "home_z"]
    assert result["position"] == {"x": 0.0, "y": 0.0, "z": 0.0}


def test_home_axes_x_y_z_to_limits_runs_x_then_y_then_z(monkeypatch):
    calls = []

    monkeypatch.setenv("APP_GRBL_Z_AXIS_ENABLED", "1")
    monkeypatch.setattr(grbl_service, "_unlock_grbl_if_needed", lambda: calls.append("unlock") or {"command": "$X"})
    monkeypatch.setattr(grbl_service, "ensure_nc_limit_pin_setting", lambda: calls.append("limits") or {"configured": False})
    monkeypatch.setattr(
        grbl_service,
        "_home_xy_axis",
        lambda axis, precheck_status=None: calls.append(f"xy_{axis}") or {"axis": axis},
    )
    monkeypatch.setattr(
        grbl_service,
        "_home_z_axis",
        lambda precheck_status=None: calls.append("z_home") or {"axis": "z"},
    )
    monkeypatch.setattr(grbl_service, "_zero_work_position", lambda include_z: calls.append(f"zero_{include_z}") or [])

    result = home_axes_x_y_z_to_limits()

    assert calls == ["unlock", "limits", "xy_x", "xy_y", "z_home", "zero_True"]
    assert result["action"] == "home_axes_x_y_z_to_limits"
    assert result["sequence"] == ["home_x", "home_y", "home_z"]
    assert result["position"] == {"x": 0.0, "y": 0.0, "z": 0.0}


def test_home_axes_to_limits_skips_z_when_z_axis_disabled(monkeypatch):
    calls = []

    monkeypatch.setenv("APP_GRBL_Z_AXIS_ENABLED", "0")
    monkeypatch.setattr(grbl_service, "_unlock_grbl_if_needed", lambda: calls.append("unlock") or {"command": "$X"})
    monkeypatch.setattr(grbl_service, "ensure_nc_limit_pin_setting", lambda: calls.append("limits") or {"configured": False})
    monkeypatch.setattr(
        grbl_service,
        "_read_homing_limit_precheck",
        lambda: calls.append("precheck") or {"limits": {"x": False, "y": False, "z": False}},
    )
    monkeypatch.setattr(grbl_service, "_get_home_xy_axis_order", lambda: ["x", "y"])
    monkeypatch.setattr(
        grbl_service,
        "_home_xy_axis",
        lambda axis, precheck_status=None: calls.append(f"xy_{axis}") or {"axis": axis},
    )
    monkeypatch.setattr(grbl_service, "_zero_work_position", lambda include_z: calls.append(f"zero_{include_z}") or [])

    result = home_axes_to_limits()

    assert calls == ["unlock", "limits", "precheck", "xy_x", "xy_y", "zero_False"]
    assert result["z_axis_enabled"] is False
    assert result["z_clearance"]["skipped"] is True
    assert result["z_report"]["skipped"] is True
    assert result["z_limit_precheck"] is None
    assert result["position"] == {"x": 0.0, "y": 0.0, "z": None}


def test_home_xy_axis_skips_motion_when_precheck_limit_is_active(monkeypatch):
    calls = []

    monkeypatch.setattr(grbl_service, "_set_arm_axis_zero", lambda axis: calls.append(f"zero_{axis}"))
    monkeypatch.setattr(grbl_service, "_run_grbl_commands", lambda *args, **kwargs: calls.append("move") or [])

    result = grbl_service._home_xy_axis(
        "x",
        precheck_status={"limits": {"x": True, "y": False, "z": False}},
    )

    assert result["already_at_limit"] is True
    assert result["limit_axes"] == ["x"]
    assert calls == ["zero_x"]


def test_home_xy_axis_requires_limit_precheck_before_motion(monkeypatch):
    calls = []

    def fake_run_grbl_commands(sequence, wait_for_idle=False, **kwargs):
        calls.append(kwargs)
        return [{"idle": {"limit_triggered": True, "limit_axes": ["x"]}}]

    monkeypatch.setenv("APP_GRBL_HOME_XY_SEARCH_DISTANCE", "10")
    monkeypatch.setenv("APP_GRBL_HOME_XY_FEED_RATE", "60")
    monkeypatch.setattr(grbl_service, "_run_grbl_commands", fake_run_grbl_commands)
    monkeypatch.setattr(grbl_service, "_set_arm_axis_zero", lambda axis: None)

    result = grbl_service._home_xy_axis(
        "x",
        precheck_status={"limits": {"x": False, "y": False, "z": False}},
    )

    assert result["stopped_by_limit"] is True
    assert calls == [
        {
            "precheck_limit_axes": {"x"},
            "observe_limit_axes": {"x"},
            "require_limit_precheck": True,
        }
    ]


def test_manual_xy_move_uses_direct_x_axis_by_default(monkeypatch):
    commands = []
    wait_flags = []

    def fake_run_grbl_commands(sequence, wait_for_idle=False, settle_delay_s=0.0, **kwargs):
        commands.extend(sequence)
        wait_flags.append(wait_for_idle)
        return [{"command": command, "wait_for_ok": wait_for_ok} for command, wait_for_ok in sequence]

    monkeypatch.setenv("APP_GRBL_MANUAL_XY_FEED_RATE", "120")
    monkeypatch.setattr(grbl_service, "_run_grbl_commands", fake_run_grbl_commands)

    result = grbl_service.manual_xy_move(1.0, 0.0)

    assert result["action"] == "manual_xy_move"
    assert commands == [("G21", True), ("G91", True), ("G1 X1.0 F120", True)]
    assert wait_flags == [True]


def test_manual_xy_move_uses_direct_y_axis_by_default(monkeypatch):
    commands = []
    wait_flags = []

    def fake_run_grbl_commands(sequence, wait_for_idle=False, settle_delay_s=0.0, **kwargs):
        commands.extend(sequence)
        wait_flags.append(wait_for_idle)
        return [{"command": command, "wait_for_ok": wait_for_ok} for command, wait_for_ok in sequence]

    monkeypatch.setenv("APP_GRBL_MANUAL_XY_FEED_RATE", "120")
    monkeypatch.setattr(grbl_service, "_run_grbl_commands", fake_run_grbl_commands)

    result = grbl_service.manual_xy_move(0.0, -2.5)

    assert result["action"] == "manual_xy_move"
    assert commands == [("G21", True), ("G91", True), ("G1 Y-2.5 F120", True)]
    assert wait_flags == [True]


def test_manual_xy_move_keeps_both_axes_when_needed(monkeypatch):
    commands = []
    wait_flags = []

    def fake_run_grbl_commands(sequence, wait_for_idle=False, settle_delay_s=0.0, **kwargs):
        commands.extend(sequence)
        wait_flags.append(wait_for_idle)
        return [{"command": command, "wait_for_ok": wait_for_ok} for command, wait_for_ok in sequence]

    monkeypatch.setenv("APP_GRBL_MANUAL_XY_FEED_RATE", "120")
    monkeypatch.setattr(grbl_service, "_run_grbl_commands", fake_run_grbl_commands)

    result = grbl_service.manual_xy_move(1.0, -2.0)

    assert result["action"] == "manual_xy_move"
    assert commands == [("G21", True), ("G91", True), ("G1 X1.0 Y-2.0 F120", True)]
    assert wait_flags == [True]


def test_manual_xy_move_rejects_zero_delta():
    with pytest.raises(grbl_service.HTTPException) as exc_info:
        grbl_service.manual_xy_move(0.0, 0.0)

    assert exc_info.value.status_code == 400


def test_manual_xy_move_clamps_to_soft_limit_after_homing(monkeypatch):
    commands = []

    def fake_run_grbl_commands(sequence, wait_for_idle=False, settle_delay_s=0.0, **kwargs):
        commands.extend(sequence)
        return [{"command": command, "wait_for_ok": wait_for_ok} for command, wait_for_ok in sequence]

    monkeypatch.setenv("APP_GRBL_MANUAL_XY_FEED_RATE", "120")
    monkeypatch.setenv("APP_GRBL_MAX_X", "4.0")
    monkeypatch.setattr(grbl_service, "_run_grbl_commands", fake_run_grbl_commands)

    grbl_service._set_arm_homed_zero()
    with grbl_service._ARM_POSITION_LOCK:
        grbl_service._ARM_XY_POSITION["x"] = 3.5

    result = grbl_service.manual_xy_move(1.0, 0.0)

    assert result["bounded_by_soft_limit"] is True
    assert result["applied_delta"] == {"x": 0.5, "y": 0.0}
    assert result["position"]["x"] == 4.0
    assert commands == [("G21", True), ("G91", True), ("G1 X0.5 F120", True)]


def test_corexy_can_be_enabled_for_a_corexy_machine(monkeypatch):
    monkeypatch.setenv("APP_GRBL_COREXY_ENABLED", "1")

    assert grbl_service._format_xy_jog_command(1.0, -2.0, 120) == "G1 X-1.0 Y3.0 F120"


def test_manual_xy_move_skips_when_soft_limit_already_reached(monkeypatch):
    commands = []

    def fake_run_grbl_commands(sequence, wait_for_idle=False, settle_delay_s=0.0, **kwargs):
        commands.extend(sequence)
        return [{"command": command, "wait_for_ok": wait_for_ok} for command, wait_for_ok in sequence]

    monkeypatch.setenv("APP_GRBL_MAX_X", "4.0")
    monkeypatch.setattr(grbl_service, "_run_grbl_commands", fake_run_grbl_commands)

    grbl_service._set_arm_homed_zero()
    with grbl_service._ARM_POSITION_LOCK:
        grbl_service._ARM_XY_POSITION["x"] = 4.0

    result = grbl_service.manual_xy_move(1.0, 0.0)

    assert result["bounded_by_soft_limit"] is True
    assert result["skipped"] is True
    assert result["results"] == []
    assert commands == []


def test_wait_for_grbl_idle_polls_until_idle(monkeypatch):
    class FakeSerial:
        def __init__(self):
            self.writes = []
            self.responses = [
                b"<Run|MPos:0.000,0.000,0.000|FS:0,0>\n",
                b"<Idle|MPos:1.000,0.000,0.000|FS:0,0>\n",
            ]

        def write(self, data):
            self.writes.append(data)

        def readline(self):
            if self.responses:
                return self.responses.pop(0)
            return b""

    monkeypatch.setenv("APP_GRBL_READ_TIMEOUT_S", "0.01")
    monkeypatch.setenv("APP_GRBL_MOTION_TIMEOUT_S", "0.2")

    fake_serial = FakeSerial()
    result = grbl_service._wait_for_grbl_idle(fake_serial)

    assert result["state"] == "Idle"
    assert fake_serial.writes == [b"?", b"?"]
    assert result["response"][-1].startswith("<Idle|")


def test_wait_for_grbl_idle_stops_when_limit_becomes_active(monkeypatch):
    class FakeSerial:
        def __init__(self):
            self.writes = []
            self.responses = [
                b"<Run|MPos:0.000,0.000,0.000|FS:60,60>\n",
                b"<Run|MPos:0.000,0.000,0.000|Pn:X|FS:60,60>\n",
            ]

        def write(self, data):
            self.writes.append(data)

        def readline(self):
            if self.responses:
                return self.responses.pop(0)
            return b""

    monkeypatch.setenv("APP_GRBL_READ_TIMEOUT_S", "0.01")
    monkeypatch.setenv("APP_GRBL_MOTION_TIMEOUT_S", "0.2")
    monkeypatch.setattr(grbl_service, "_stop_grbl_motion_for_limit", lambda ser: {"stopped": True})

    fake_serial = FakeSerial()
    result = grbl_service._wait_for_grbl_idle(fake_serial, moving_limit_axes={"x"}, initial_limit_axes=set())

    assert result["limit_triggered"] is True
    assert result["limit_axes"] == ["x"]
    assert result["stop"] == {"stopped": True}


def test_run_grbl_commands_reuses_existing_serial_connection(monkeypatch):
    created_serials = []
    startup_calls = []
    sent_commands = []

    class FakeSerial:
        def __init__(self):
            self.port = None
            self.baudrate = None
            self.timeout = None
            self.dtr = True
            self.rts = True
            self.is_open = False
            created_serials.append(self)

        def open(self):
            self.is_open = True

        def close(self):
            self.is_open = False

        def reset_input_buffer(self):
            return None

        def reset_output_buffer(self):
            return None

    def fake_prepare_grbl_serial(ser):
        startup_calls.append(ser)
        return ["Grbl ready"]

    def fake_send_grbl_on_serial(ser, command, wait_for_ok=True):
        sent_commands.append((ser, command, wait_for_ok))
        return {"command": command, "wait_for_ok": wait_for_ok}

    grbl_service._close_grbl_serial()
    monkeypatch.setattr(grbl_service.serial, "Serial", FakeSerial)
    monkeypatch.setattr(grbl_service, "_prepare_grbl_serial", fake_prepare_grbl_serial)
    monkeypatch.setattr(grbl_service, "_send_grbl_on_serial", fake_send_grbl_on_serial)

    try:
        first = grbl_service._run_grbl_commands([("G21", True)])
        second = grbl_service._run_grbl_commands([("G91", True)])
    finally:
        grbl_service._close_grbl_serial()

    assert len(created_serials) == 1
    assert startup_calls == [created_serials[0]]
    assert sent_commands == [
        (created_serials[0], "G21", True),
        (created_serials[0], "G91", True),
    ]
    assert first[0]["startup"] == ["Grbl ready"]
    assert "startup" not in second[0]


def test_run_grbl_commands_falls_back_to_detected_grbl_port(monkeypatch):
    created_serials = []
    sent_commands = []

    class FakeSerial:
        def __init__(self):
            self.port = None
            self.baudrate = None
            self.timeout = None
            self.dtr = True
            self.rts = True
            self.is_open = False
            self.writes = []
            created_serials.append(self)

        def open(self):
            self.is_open = True

        def close(self):
            self.is_open = False

        def reset_input_buffer(self):
            return None

        def reset_output_buffer(self):
            return None

        def write(self, data):
            self.writes.append(data)

        def readline(self):
            if self.port == "/dev/ttyUSB1" and self.writes and self.writes[-1] == b"?":
                return b"<Idle|MPos:0.000,0.000,0.000|FS:0,0>\n"
            return b""

    def fake_glob(pattern):
        if pattern == "/dev/ttyUSB*":
            return ["/dev/ttyUSB0", "/dev/ttyUSB1"]
        return []

    def fake_send_grbl_on_serial(ser, command, wait_for_ok=True):
        sent_commands.append((ser.port, command, wait_for_ok))
        return {"command": command, "wait_for_ok": wait_for_ok}

    grbl_service._close_grbl_serial()
    monkeypatch.setenv("APP_GRBL_PORT", "/dev/missing")
    monkeypatch.setattr(grbl_service.glob, "glob", fake_glob)
    monkeypatch.setattr(grbl_service.os.path, "exists", lambda port: True)
    monkeypatch.setattr(grbl_service.serial, "Serial", FakeSerial)
    monkeypatch.setattr(grbl_service, "_prepare_grbl_serial", lambda ser: [])
    monkeypatch.setattr(grbl_service, "_send_grbl_on_serial", fake_send_grbl_on_serial)

    try:
        grbl_service._run_grbl_commands([("G21", True)])
    finally:
        grbl_service._close_grbl_serial()

    assert [ser.port for ser in created_serials] == ["/dev/missing", "/dev/ttyUSB0", "/dev/ttyUSB1"]
    assert sent_commands == [("/dev/ttyUSB1", "G21", True)]
