Tbo-s/sya_ai-scanner/code/picode/visionAI/backend/services/scan_orchestrator.py

from __future__ import annotations

import asyncio
import os
import uuid
from dataclasses import dataclass, field
from typing import Optional

from fastapi import HTTPException


class FlowState:
    BOOT = "BOOT"
    WELCOME = "WELCOME"
    IMEI_SCAN = "IMEI_SCAN"
    DEVICE_LOOKUP = "DEVICE_LOOKUP"
    WAIT_POWER_OFF = "WAIT_POWER_OFF"
    LOAD_DEVICE = "LOAD_DEVICE"
    CLOSE_BOX = "CLOSE_BOX"
    CAPTURE_FRONT = "CAPTURE_FRONT"
    CAPTURE_BACK = "CAPTURE_BACK"
    UPLOAD_RESULTS = "UPLOAD_RESULTS"
    RETURN_DEVICE = "RETURN_DEVICE"
    SHOW_PRICE = "SHOW_PRICE"
    DONE = "DONE"
    ERROR = "ERROR"
    EMERGENCY_STOP = "EMERGENCY_STOP"


@dataclass
class ScanSession:
    session_id: str
    imei: str
    device_model: str
    max_value_eur: float
    photo_paths: list[str] = field(default_factory=list)
    ai_result: Optional[dict] = None
    upload_result: Optional[dict] = None
    status: str = "running"
    state: str = FlowState.LOAD_DEVICE
    current_step: int = 0
    error: Optional[str] = None


class ScanOrchestrator:
    def __init__(self, connection_manager):
        self.connection_manager = connection_manager
        self.current_session: Optional[ScanSession] = None
        self._task: Optional[asyncio.Task] = None
        self._user_event = asyncio.Event()

    async def start_scan(self, imei: str, device_model: str, max_value_eur: float) -> ScanSession:
        if self._task and not self._task.done():
            raise HTTPException(status_code=409, detail="A scan is already in progress.")

        session = ScanSession(
            session_id=str(uuid.uuid4()),
            imei=imei,
            device_model=device_model,
            max_value_eur=max_value_eur,
        )
        self.current_session = session
        self._user_event.clear()
        self._task = asyncio.create_task(self._run_sequence(session))
        return session

    async def confirm_user_action(self):
        if not self.current_session or self.current_session.status != "awaiting_user":
            raise HTTPException(status_code=409, detail="No scan is waiting for confirmation.")
        self._user_event.set()

    async def emergency_abort(self):
        if self._task and not self._task.done():
            self._task.cancel()
            try:
                await self._task
            except asyncio.CancelledError:
                pass

        await asyncio.to_thread(self._hw_emergency_stop)
        if self.current_session:
            self.current_session.status = "failed"
            self.current_session.state = FlowState.EMERGENCY_STOP
            self.current_session.error = "emergency_abort"
        await self._broadcast(
            "scan_failed",
            0,
            "emergency_abort",
            {"reason": "abort"},
            state=FlowState.EMERGENCY_STOP,
        )

    def get_status(self) -> Optional[dict]:
        if not self.current_session:
            return None
        session = self.current_session
        return {
            "session_id": session.session_id,
            "status": session.status,
            "state": session.state,
            "current_step": session.current_step,
            "imei": session.imei,
            "device_model": session.device_model,
            "max_value_eur": session.max_value_eur,
            "photo_count": len(session.photo_paths),
            "ai_result": session.ai_result,
            "upload_result": session.upload_result,
            "error": session.error,
        }

    @staticmethod
    def _hw_emergency_stop():
        try:
            from services import grbl_service, machine_service

            machine_service.vacuum_off(raise_on_no_ack=False)
            machine_service.emergency_stop()
            grbl_service.feed_hold()
        except Exception:
            pass

    async def _broadcast(
        self,
        event_type: str,
        step: int,
        step_name: str,
        data: dict,
        state: Optional[str] = None,
    ):
        current_state = state or (self.current_session.state if self.current_session else "")
        payload = {
            "scan_event": {
                "type": event_type,
                "state": current_state,
                "step": step,
                "step_name": step_name,
                "data": {"state": current_state, **data},
            }
        }
        try:
            await self.connection_manager.broadcast(payload)
        except Exception:
            pass

    async def _run_sequence(self, session: ScanSession):
        try:
            await self._execute_sequence(session)
        except asyncio.CancelledError:
            session.status = "failed"
            session.state = FlowState.ERROR
            session.error = "cancelled"
            raise
        except Exception as exc:
            session.status = "failed"
            session.state = FlowState.ERROR
            session.error = str(exc)
            await self._broadcast(
                "scan_failed",
                session.current_step,
                "error",
                {"error": str(exc)},
                state=FlowState.ERROR,
            )
            await asyncio.to_thread(self._hw_emergency_stop)

    async def _set_state(self, session: ScanSession, state: str, data: Optional[dict] = None):
        session.state = state
        await self._broadcast("state_changed", session.current_step, state.lower(), data or {}, state=state)

    async def _step(self, session: ScanSession, step_num: int, step_name: str, fn, *args, **kwargs):
        session.current_step = step_num
        result = await asyncio.to_thread(fn, *args, **kwargs)
        await self._broadcast("step_complete", step_num, step_name, result if isinstance(result, dict) else {})
        return result

    async def _await_user(self, session: ScanSession, step_num: int, step_name: str, message: str):
        session.status = "awaiting_user"
        session.current_step = step_num
        self._user_event.clear()
        await self._broadcast("awaiting_user", step_num, step_name, {"message": message}, state=session.state)
        timeout = float(os.getenv("APP_USER_CONFIRM_TIMEOUT_S", "300"))
        try:
            await asyncio.wait_for(self._user_event.wait(), timeout=timeout)
        except asyncio.TimeoutError as exc:
            raise RuntimeError(f"User confirmation timeout at step {step_num}") from exc
        session.status = "running"
        self._user_event.clear()

    async def _execute_sequence(self, session: ScanSession):
        from controller.camera import camera_manager, take_photo
        from services import ai_damage_service, grbl_service, machine_service, scan_upload_service

        vacuum_dwell = float(os.getenv("APP_VACUUM_DWELL_S", "1.0"))

        await self._set_state(session, FlowState.LOAD_DEVICE)
        await self._step(session, 19, "gate_open", machine_service.open_gate)
        await self._step(session, 19, "gate_open_wait", machine_service.wait_for_gate_done)
        await self._step(session, 20, "tray_out", machine_service.tray_out)
        await self._step(session, 20, "tray_out_wait", machine_service.wait_for_tray_done)
        await self._await_user(session, 21, "phone_added_check", "Toestel toegevoegd?")

        await self._set_state(session, FlowState.CLOSE_BOX)
        await self._step(session, 23, "tray_in", machine_service.tray_in)
        await self._step(session, 23, "tray_in_wait", machine_service.wait_for_tray_done)
        await self._step(session, 24, "gate_close", machine_service.close_gate)
        await self._step(session, 24, "gate_close_wait", machine_service.wait_for_gate_done)

        await self._set_state(session, FlowState.CAPTURE_FRONT)
        await self._step(session, 25, "arm_approach_front", grbl_service.move_to_front_slow_with_distance_stop)
        await self._step(session, 27, "vacuum_on", machine_service.vacuum_on)
        await asyncio.sleep(vacuum_dwell)
        await self._step(session, 28, "z_up", grbl_service.z_up)
        await self._step(session, 29, "tray_to_gate", machine_service.tray_to_gate_position)
        await self._step(session, 29, "tray_to_gate_wait", machine_service.wait_for_tray_done)
        await asyncio.to_thread(camera_manager.start)
        await asyncio.to_thread(camera_manager.wait_for_frame, 5.0)
        wrist2_min = machine_service.wrist_min_angle(2)
        wrist2_max = machine_service.wrist_max_angle(2)
        wrist1_max = machine_service.wrist_max_angle(1)
        wrist1_home = machine_service.wrist1_home_angle()
        await self._step(session, 30, "wrist1_neutral", machine_service.set_wrist1, wrist1_home)

        for step_num, label in ((31, "front_side_1"), (33, "front_side_2"), (35, "front_side_3")):
            result = await asyncio.to_thread(take_photo, label, session.session_id)
            session.photo_paths.append(result["path"])
            await self._broadcast("step_complete", step_num, f"photo_{label}", result)
            if step_num == 31:
                await self._step(session, 32, "wrist2_neg90", machine_service.set_wrist2, wrist2_min)
            elif step_num == 33:
                await self._step(session, 34, "wrist2_pos90", machine_service.set_wrist2, wrist2_max)

        await self._step(session, 36, "wrist1_pos90", machine_service.set_wrist1, wrist1_max)
        await self._step(session, 37, "tray_center", machine_service.tray_in)
        await self._step(session, 37, "tray_center_wait", machine_service.wait_for_tray_done)
        await self._step(session, 38, "wrist_home", machine_service.wrist_home)
        await self._step(session, 39, "z_down", grbl_service.z_down)
        await self._step(session, 40, "vacuum_off", machine_service.vacuum_off)

        await self._set_state(session, FlowState.CAPTURE_BACK)
        await self._step(session, 41, "arm_to_back_rapid", grbl_service.move_to_back_of_phone)
        await self._step(session, 42, "arm_approach_back", grbl_service.move_to_back_slow_with_distance_stop)
        await self._step(session, 43, "vacuum_on_back", machine_service.vacuum_on)
        await asyncio.sleep(vacuum_dwell)
        await self._step(session, 44, "z_up_back", grbl_service.z_up)
        await self._step(session, 45, "tray_to_gate_back", machine_service.tray_to_gate_position)
        await self._step(session, 45, "tray_to_gate_back_wait", machine_service.wait_for_tray_done)
        await self._step(session, 46, "wrist1_neutral_back", machine_service.set_wrist1, wrist1_home)

        for step_num, label in ((47, "back_side_1"), (49, "back_side_2"), (51, "back_side_3")):
            result = await asyncio.to_thread(take_photo, label, session.session_id)
            session.photo_paths.append(result["path"])
            await self._broadcast("step_complete", step_num, f"photo_{label}", result)
            if step_num == 47:
                await self._step(session, 48, "wrist2_neg90_back", machine_service.set_wrist2, wrist2_min)
            elif step_num == 49:
                await self._step(session, 50, "wrist2_pos90_back", machine_service.set_wrist2, wrist2_max)

        await self._step(session, 52, "wrist1_pos90_back", machine_service.set_wrist1, wrist1_max)
        await self._set_state(session, FlowState.UPLOAD_RESULTS)
        session.current_step = 53
        await self._broadcast("step_complete", 53, "ai_analyzing", {"photo_count": len(session.photo_paths)})
        ai_result = await asyncio.to_thread(
            ai_damage_service.analyze_photos,
            session.imei,
            session.session_id,
            session.photo_paths,
            session.max_value_eur,
        )
        session.ai_result = ai_result.model_dump()
        await self._broadcast("step_complete", 53, "ai_done", session.ai_result)
        upload_result = await asyncio.to_thread(
            scan_upload_service.upload_scan_results,
            imei=session.imei,
            session_id=session.session_id,
            device_model=session.device_model,
            max_value_eur=session.max_value_eur,
            photo_paths=session.photo_paths,
            ai_result=session.ai_result,
        )
        session.upload_result = upload_result
        await self._broadcast("step_complete", 53, "scan_upload", upload_result)

        await self._set_state(session, FlowState.RETURN_DEVICE)
        await self._step(session, 54, "tray_center_back", machine_service.tray_in)
        await self._step(session, 54, "tray_center_back_wait", machine_service.wait_for_tray_done)
        await self._step(session, 55, "wrist_home_back", machine_service.wrist_home)
        await self._step(session, 56, "z_down_back", grbl_service.z_down)
        await self._step(session, 57, "vacuum_off_back", machine_service.vacuum_off)
        await self._step(session, 58, "gate_open_return", machine_service.open_gate)
        await self._step(session, 58, "gate_open_return_wait", machine_service.wait_for_gate_done)
        await self._step(session, 59, "tray_out_return", machine_service.tray_out)
        await self._step(session, 59, "tray_out_return_wait", machine_service.wait_for_tray_done)
        session.status = "complete"
        session.state = FlowState.SHOW_PRICE
        session.current_step = 60
        await self._broadcast(
            "scan_complete",
            60,
            "phone_retrieval",
            {"ai_result": session.ai_result},
            state=FlowState.SHOW_PRICE,
        )
